allanschwartz/yahrzeit/presentations/yahrzeit_presentation 2015-07-27.pdf

## Yahrzeit Wall Overview

at

## Congregation Beth Sholom

## Yahrzeit/Yizkor presentation

■ | What is a Yahrzeit? What is a Yikzor observance?
■ | Traditional yahrzeit fixtures
■ | New Cong. Beth Sholom requirements:
■ | Ultra-modern building design
■ | Yahrzeit wall, as a architectural entity
■ | Automation, hands free operation
■ | Yahrzeit wall functionality
■ | Yahrzeit Wall is comprised of
■ | Glass Panels
■ | Yahrzeit server software with database and automation
■ | Yahrzeit panel embedded electronics / light modules

## Yahrzeit/Yizkor

■ | A Yahrzeit (yiddish) means time-(of)-year, is the yearly observation of a loved ones’ passing. Rabbinic custom is to say kaddish on the yahrzeit, (or the service immediately before that date), and the mourners often light a 24-hour yahrzeit candle. In addition, the synagogue may light a lamp for the week including the preceeding the Shabbat. These lamps are in yahrzeit fixtures.
■ | On four special yizkor observances per year, all the yahrzeit lamps are illuminating, during the yizkor service. (Yom Kippur, Shmini Atzeret, on the last day of Passover, and on Shavuot). Sometimes we also observe Yom Hazikaron (4th Iyar) and/or Yom Hashoah (27th Nisan).

## Traditional yahrzeit fixtures

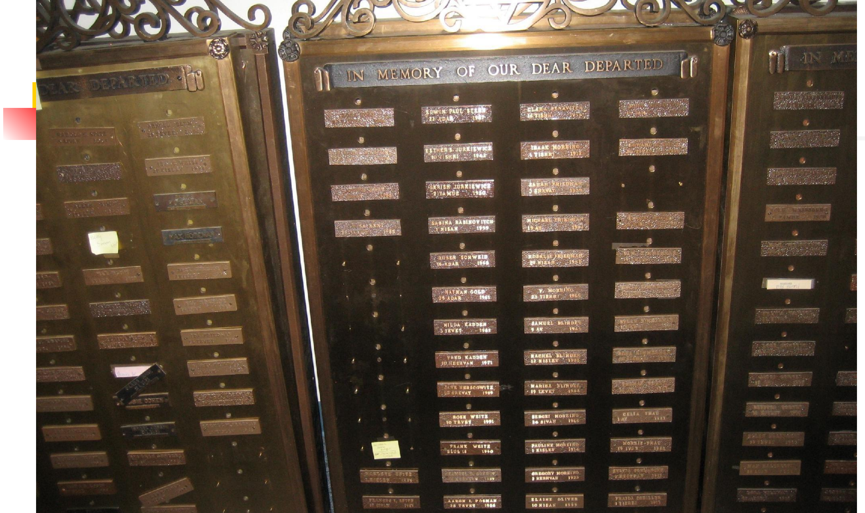
[picture p63: page 4]

## New Cong. Beth Sholom Requirements

## ■ Ultra-modern building design ■ East side of sanctuary has unique features

■ West wall of sanctuary, “Yahrzeit Wall”,

## complements the east wall ■ Etched glass panels appear to float ■ Fully automated LED lamps behind up to 2400 etched names

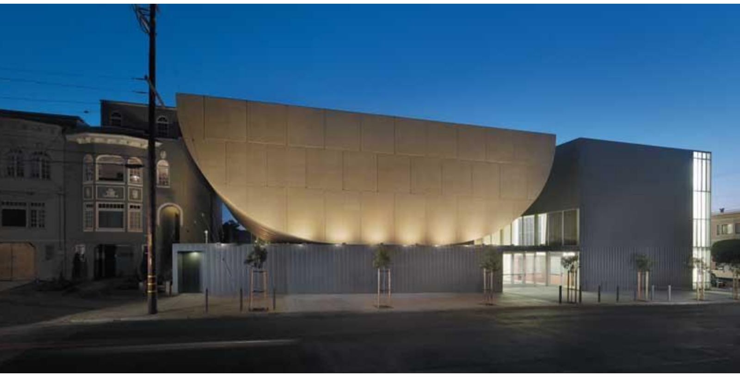
[picture p64: page 6]
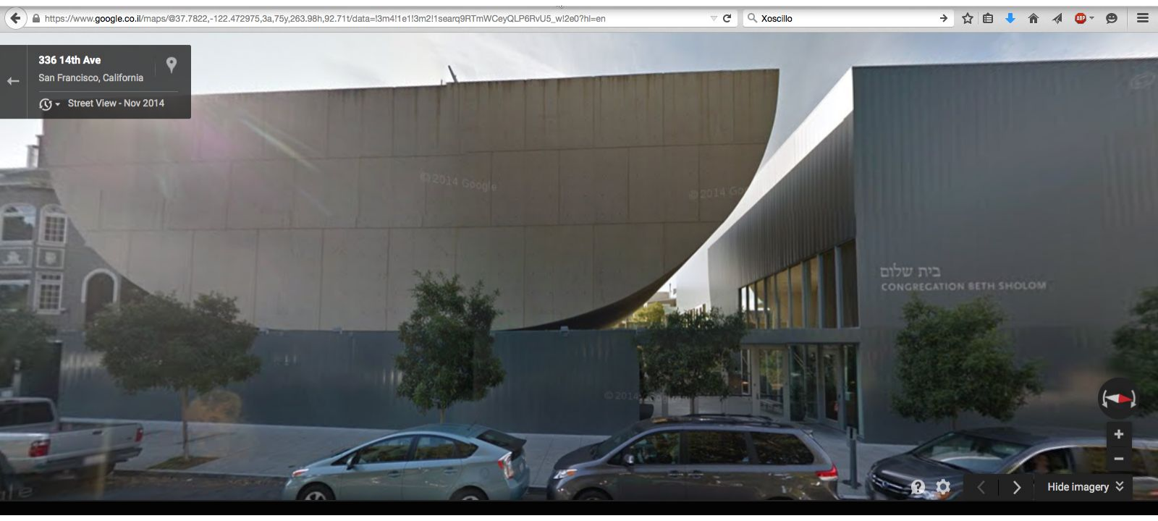
[picture p65: page 7]
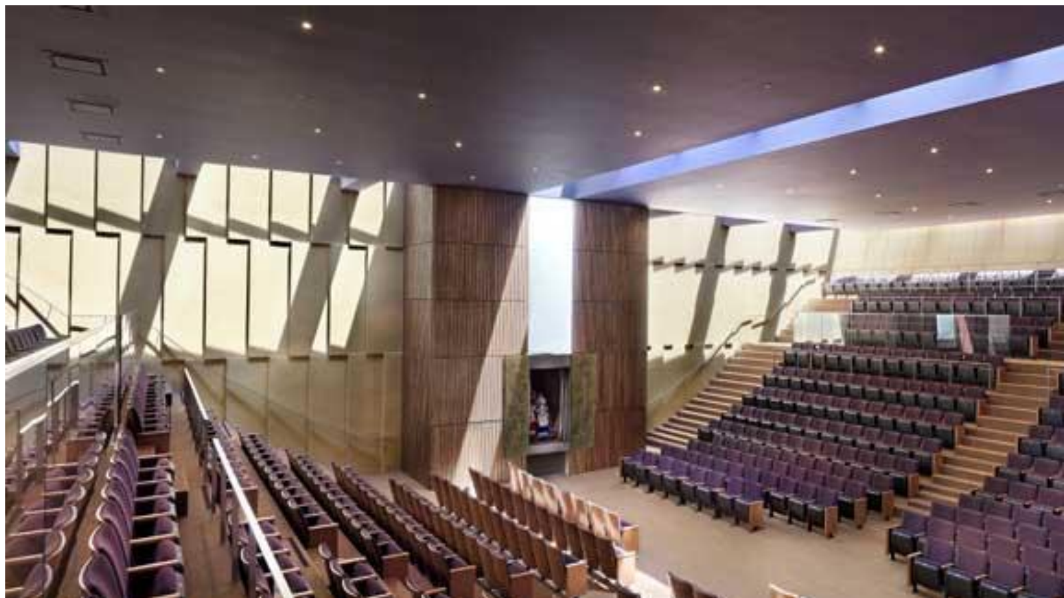
[picture p66: page 8]
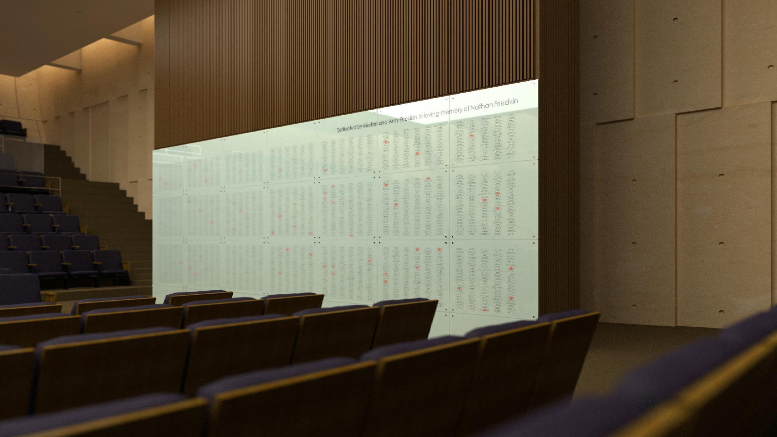
[picture p67: page 9]
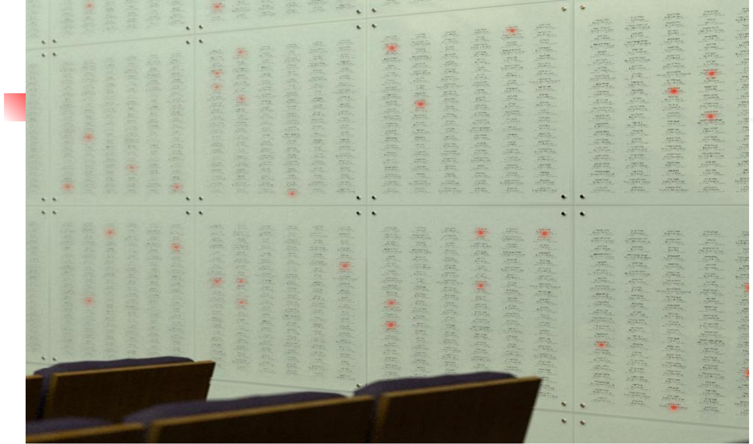
[picture p68: page 10]

# Yahrzeit Wall design goals

## ■ Simplicity & Elegance ■ Ease of use & no maintenance ■ Full database integration & automation ■ Future proof

# Yahrzeit Wall components

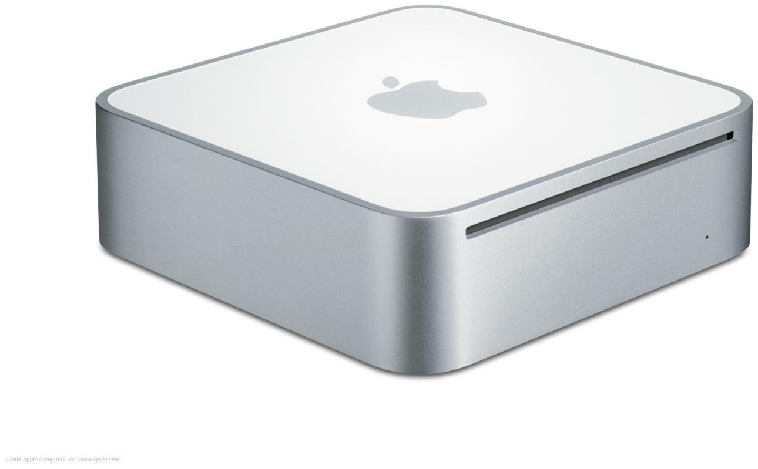
[picture p69: figure]
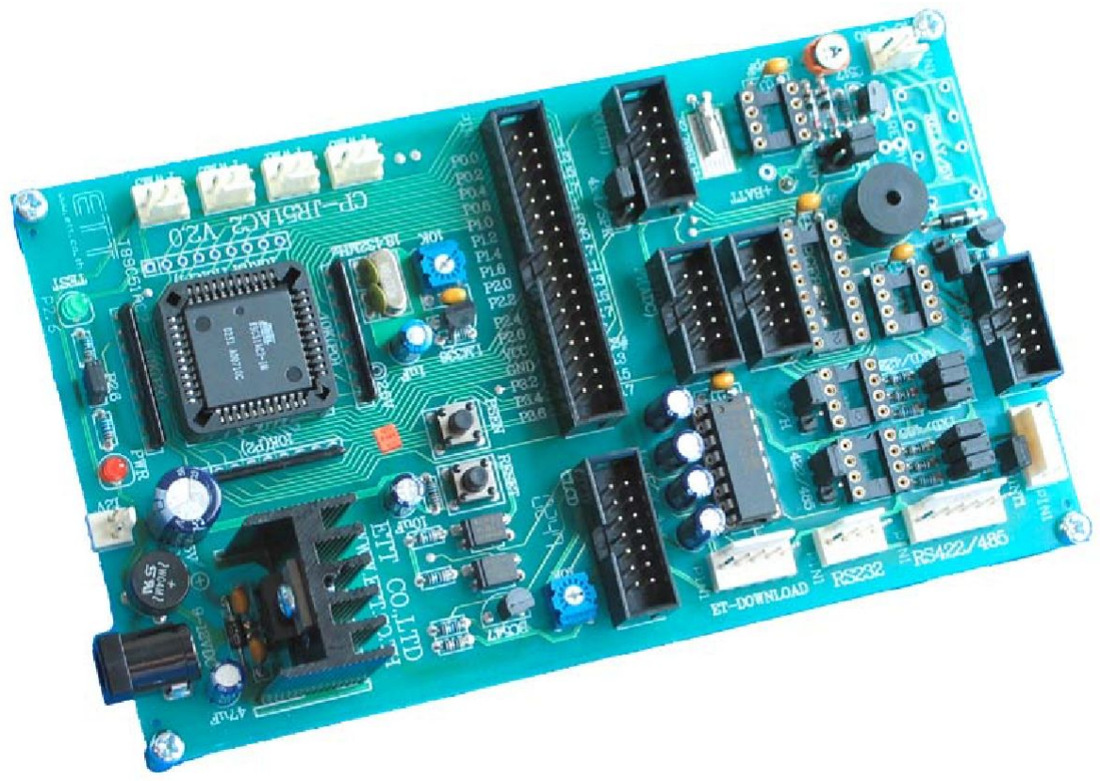
[picture p70: figure]
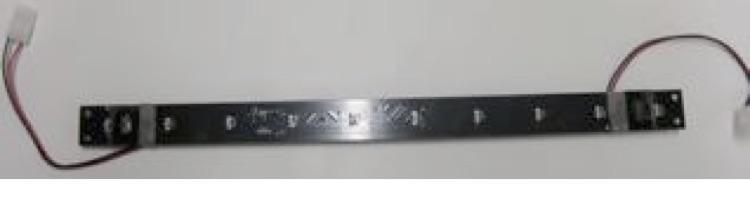
[picture p71: figure]
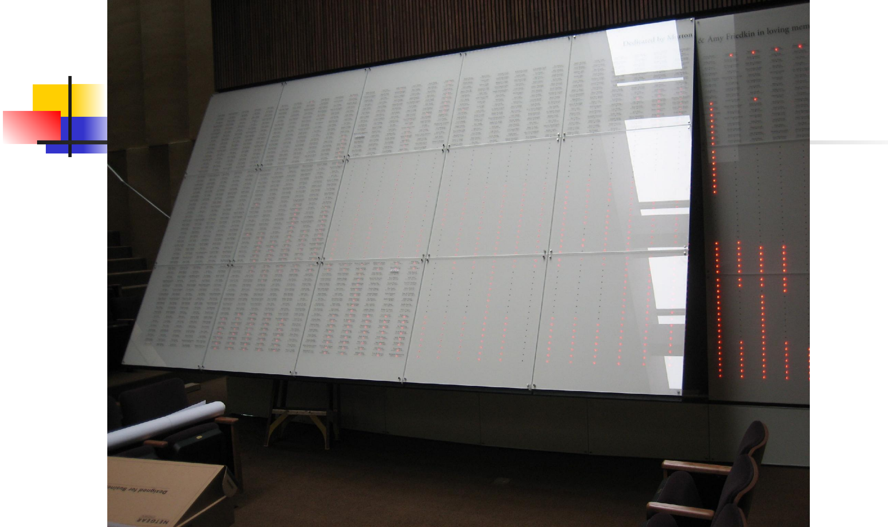
[picture p72: page 13]
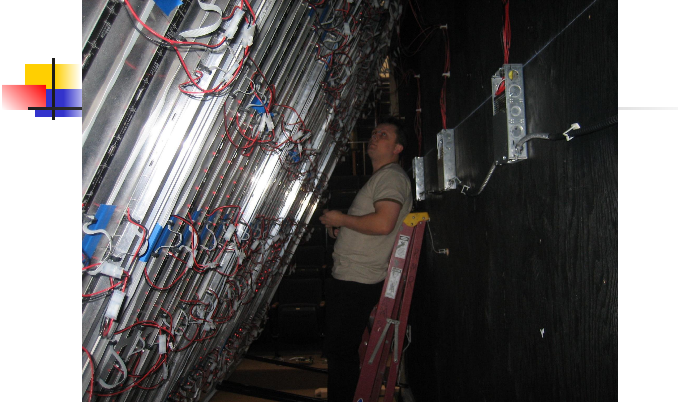
[picture p73: page 14]

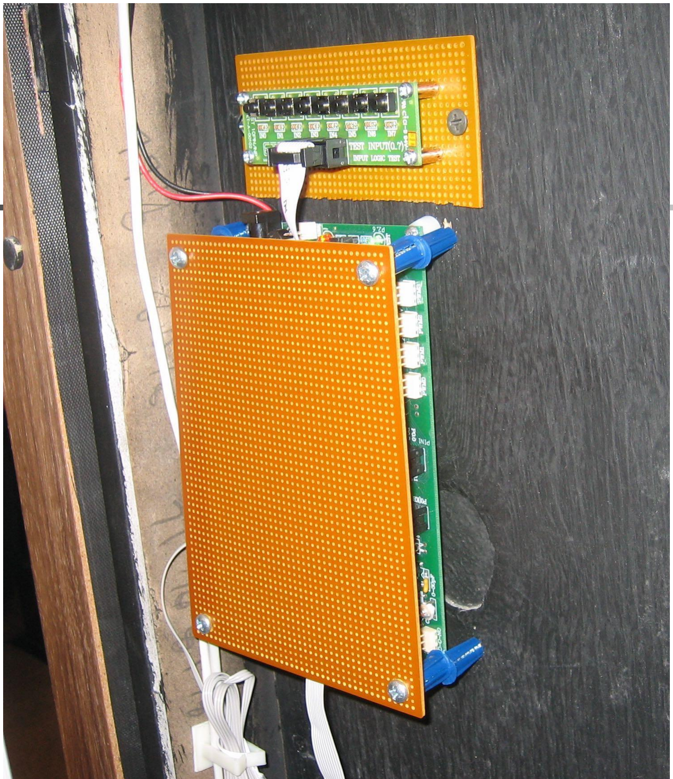
[picture p74: figure]

# Yahrzeit V2 (2015) components

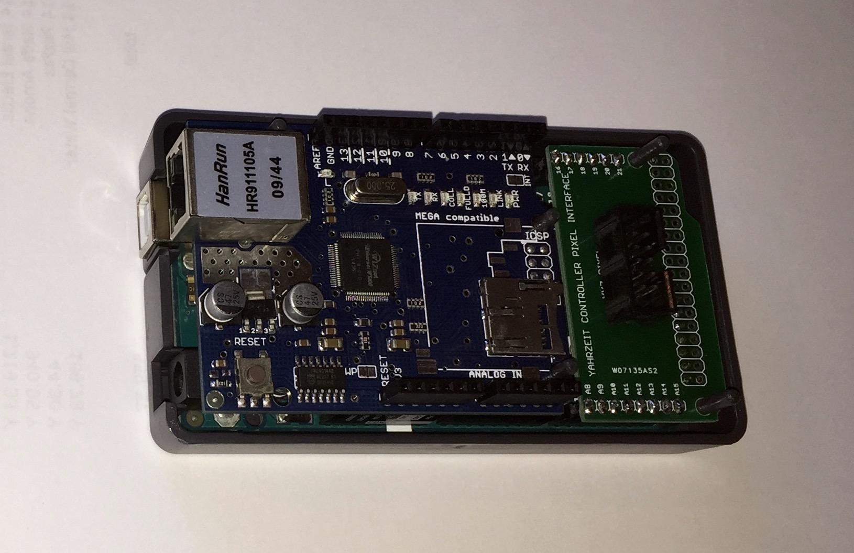
[picture p75: figure]
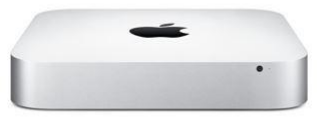
[picture p76: figure]

## Yahrzeit controller software

## ■ Jewish-calendar based yahrzeit light automation ■ Ability to maintain the memorial database ■ Customize yahrzeit observance for any name ■ Customize the synagogues yahrzeit and yizkor observances based on Conservative / Orthodox / Reform minhag

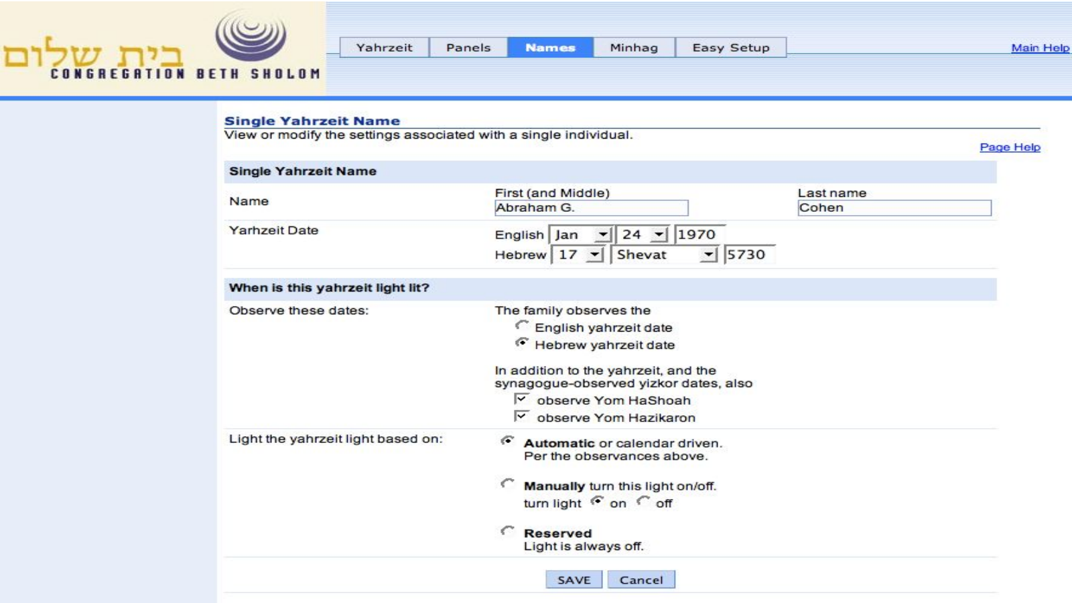
[picture p77: page 18]
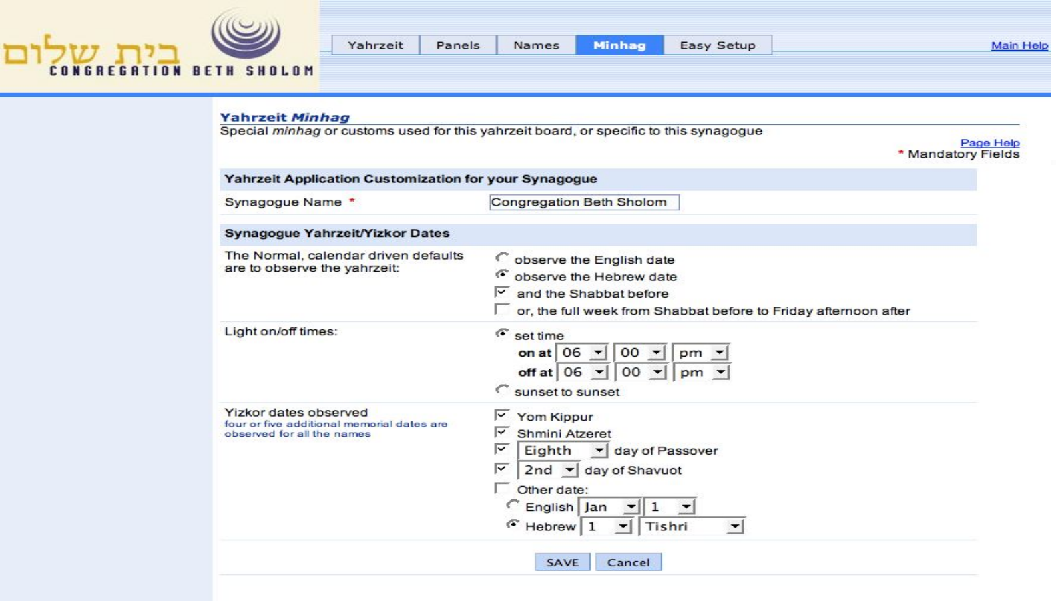
[picture p78: page 19]
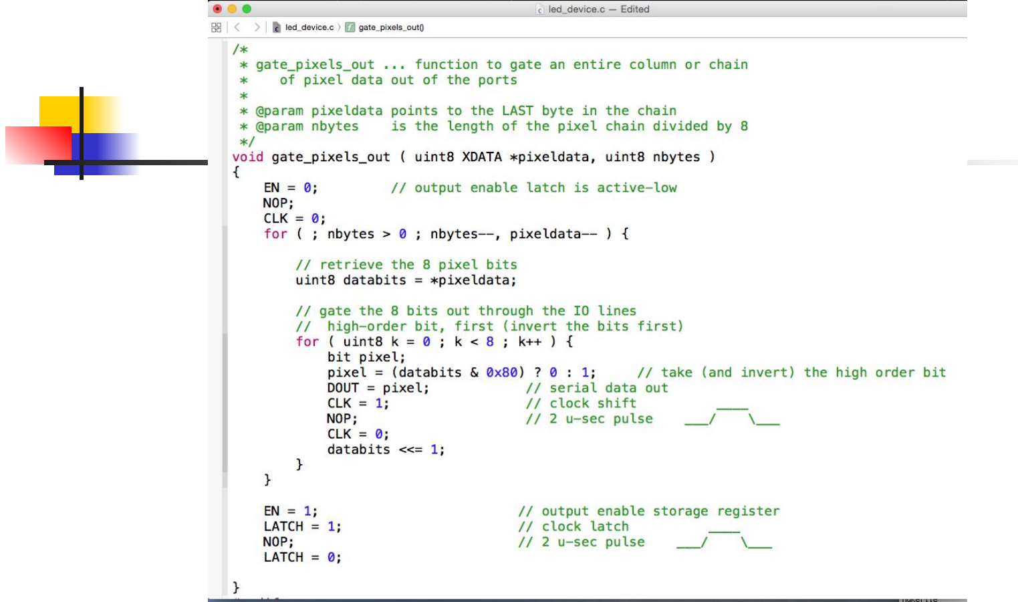
[picture p79: page 20]
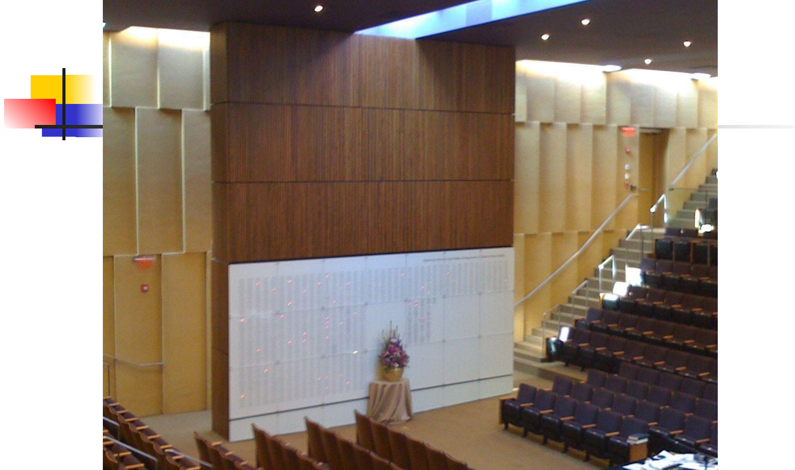
[picture p80: page 21]
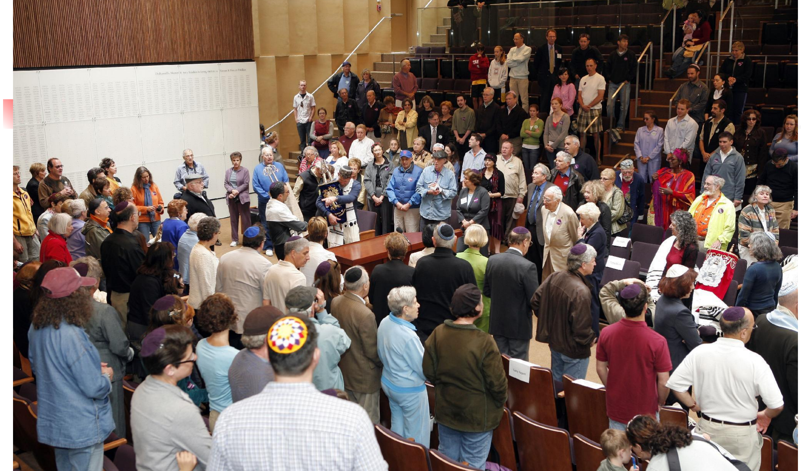
[picture p81: page 22]
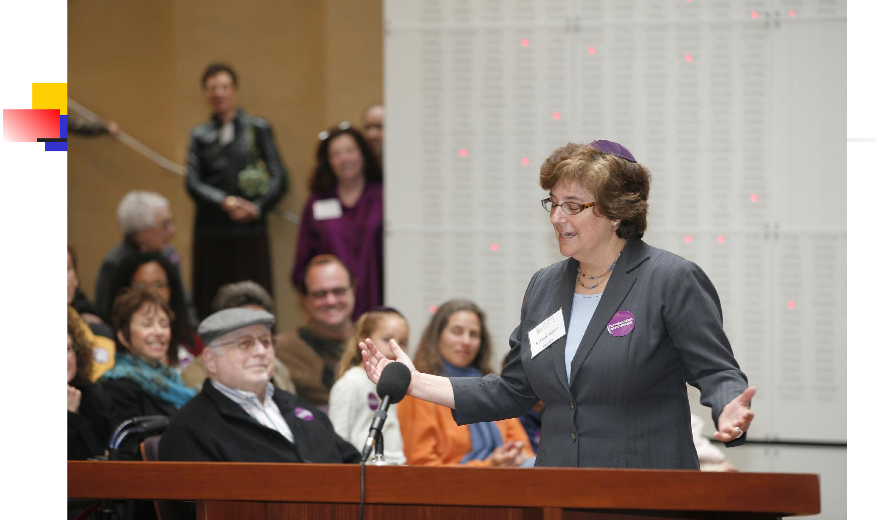
[picture p82: page 23]
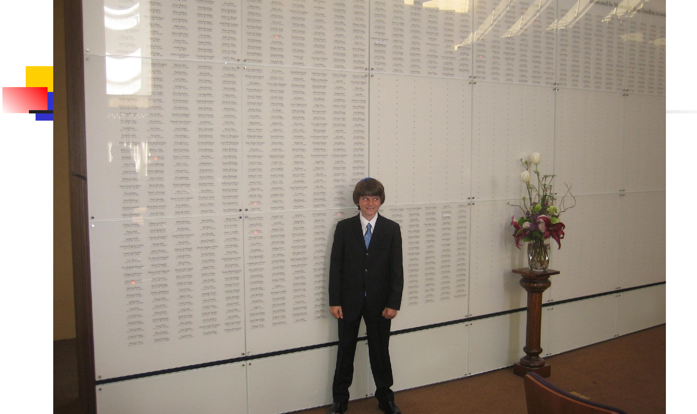
[picture p83: page 24]

# Thank you

## ■ Sources at: ■ https://github.com/allanschwartz/yahrzeit
