allanschwartz/yahrzeit/presentations/presentation_images_used/T89C51 Training Board - V5.pdf

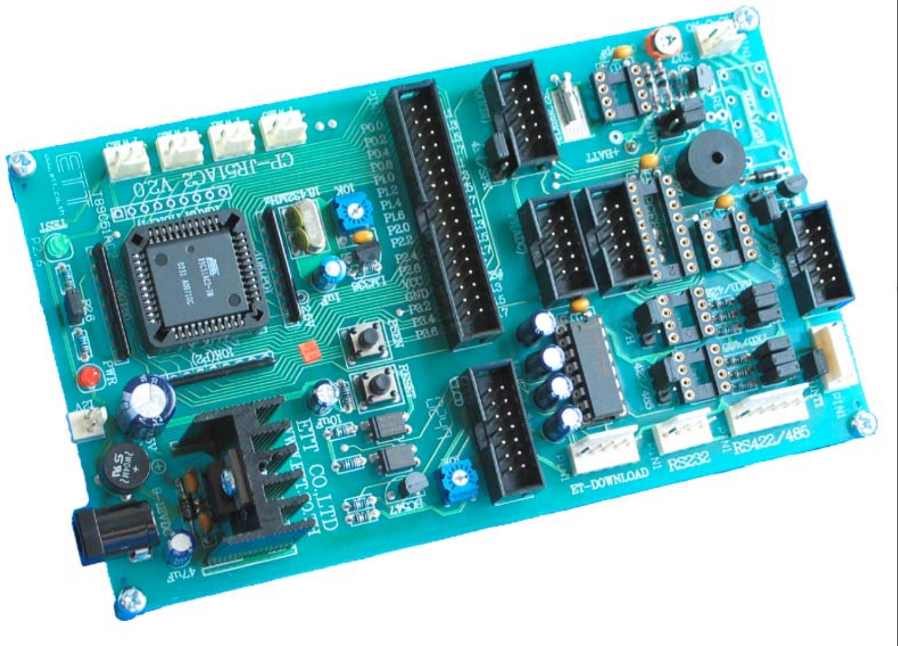
[picture p84: page 1]
