allanschwartz/yahrzeit/Hardware/cables/molex_5559-03P.JPG

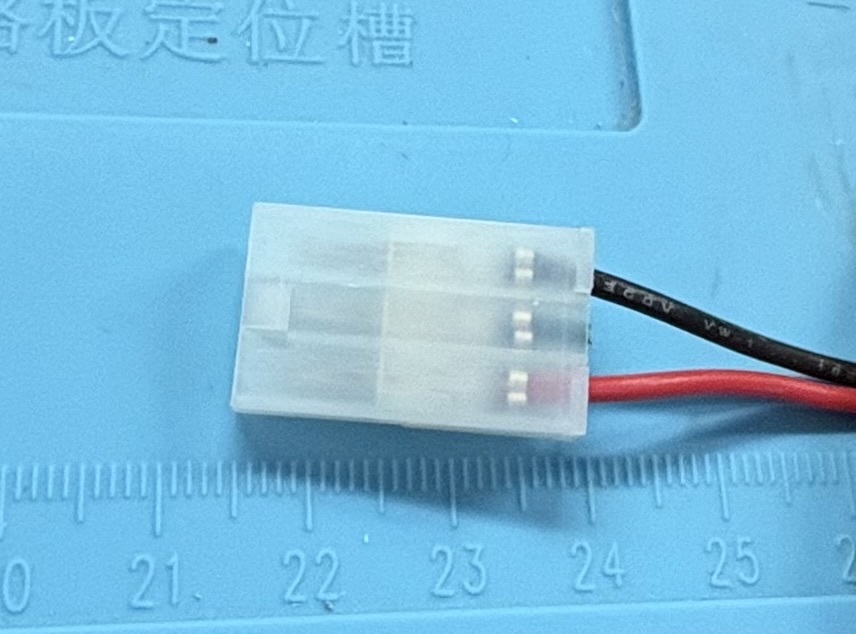
Hardware/cables/molex_5559-03P.JPG
