allanschwartz/yahrzeit/Hardware/pixel_interface_v3/pixel_interface_v3-schematic.png

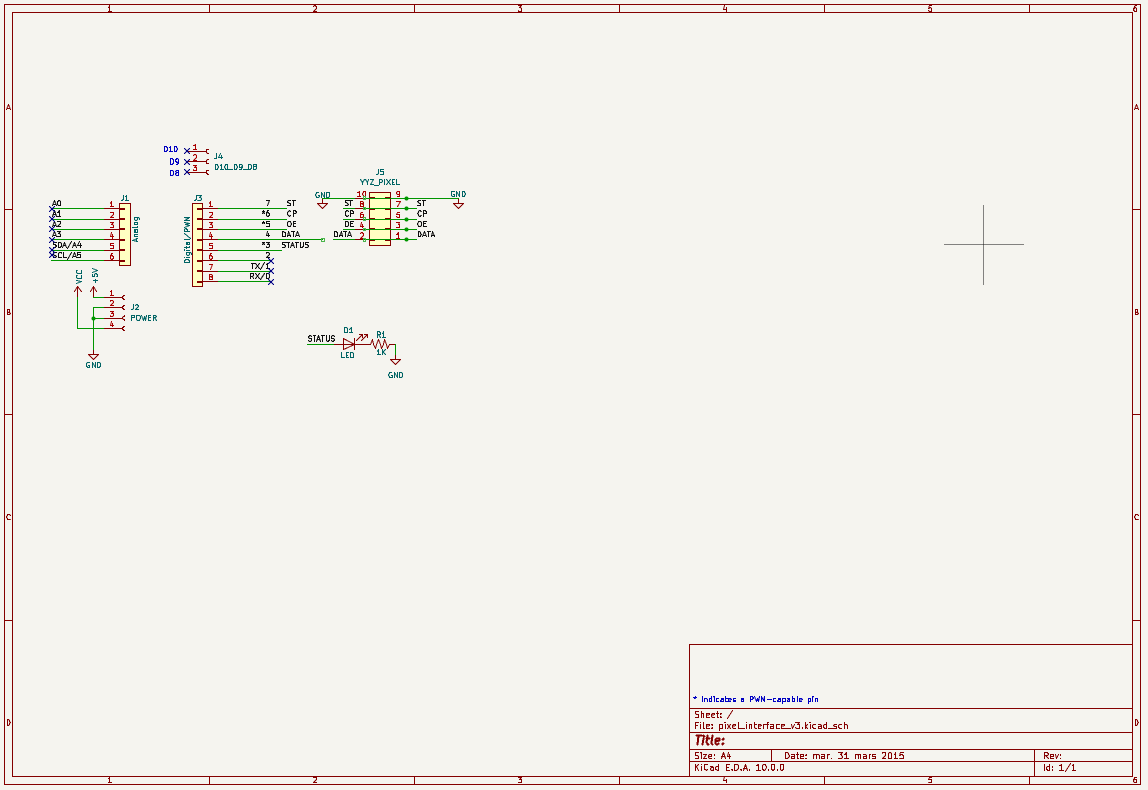
Hardware/pixel_interface_v3/pixel_interface_v3-schematic.png
