allanschwartz/yahrzeit/Hardware/YYZ_SHIELD_v2/arduino_shield.PNG

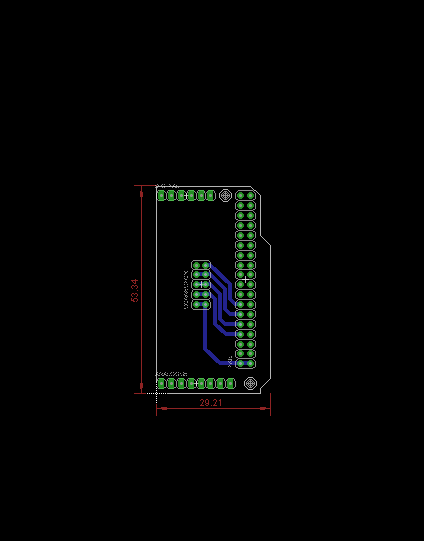
Hardware/YYZ_SHIELD_v2/arduino_shield.PNG
