allanschwartz/yahrzeit/Hardware/YYZ_SHIELD_v2/prototype assm2.jpg

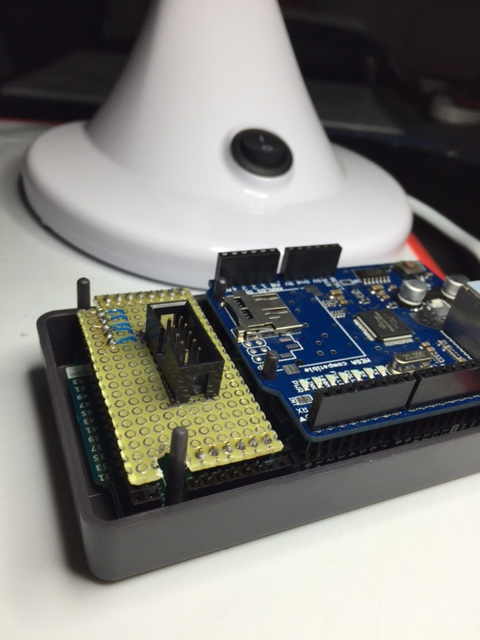
Hardware/YYZ_SHIELD_v2/prototype assm2.jpg
