allanschwartz/yahrzeit/Hardware/YYZ_SHIELD_v2/prototype tail shield.JPG

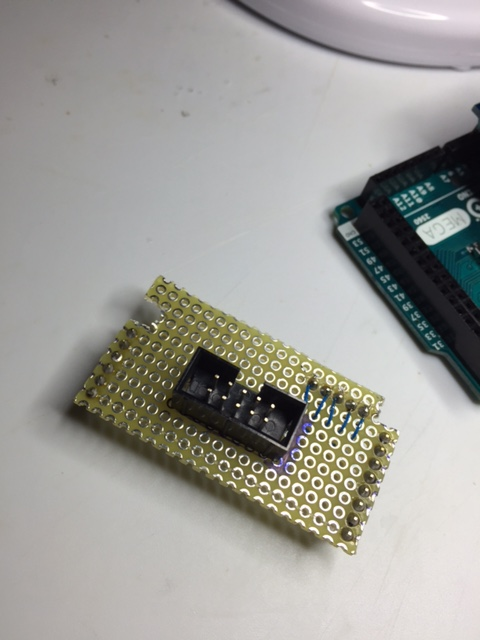
Hardware/YYZ_SHIELD_v2/prototype tail shield.JPG
