allanschwartz/yahrzeit/Hardware/YYZ_SHIELD_v2/shield modified.PNG

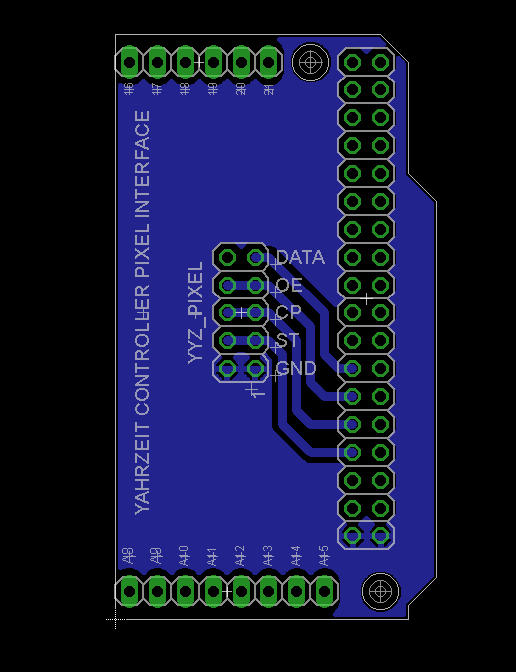
Hardware/YYZ_SHIELD_v2/shield modified.PNG
