allanschwartz/yahrzeit/Hardware/YYZ_SHIELD_v2/yarhzeit_adapter_shield_bb.jpg

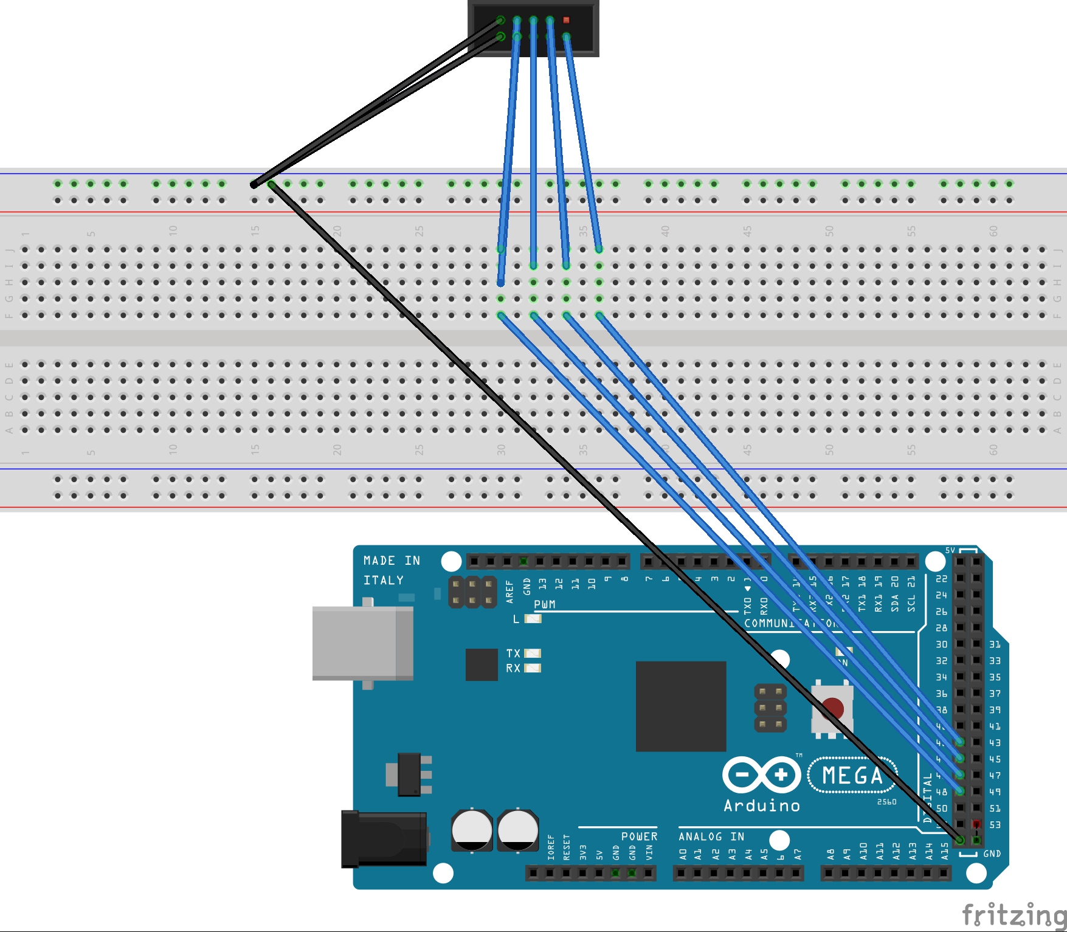
Hardware/YYZ_SHIELD_v2/yarhzeit_adapter_shield_bb.jpg
