allanschwartz/yahrzeit/presentations/other_images/finished yahrzeit embedded controller.jpg

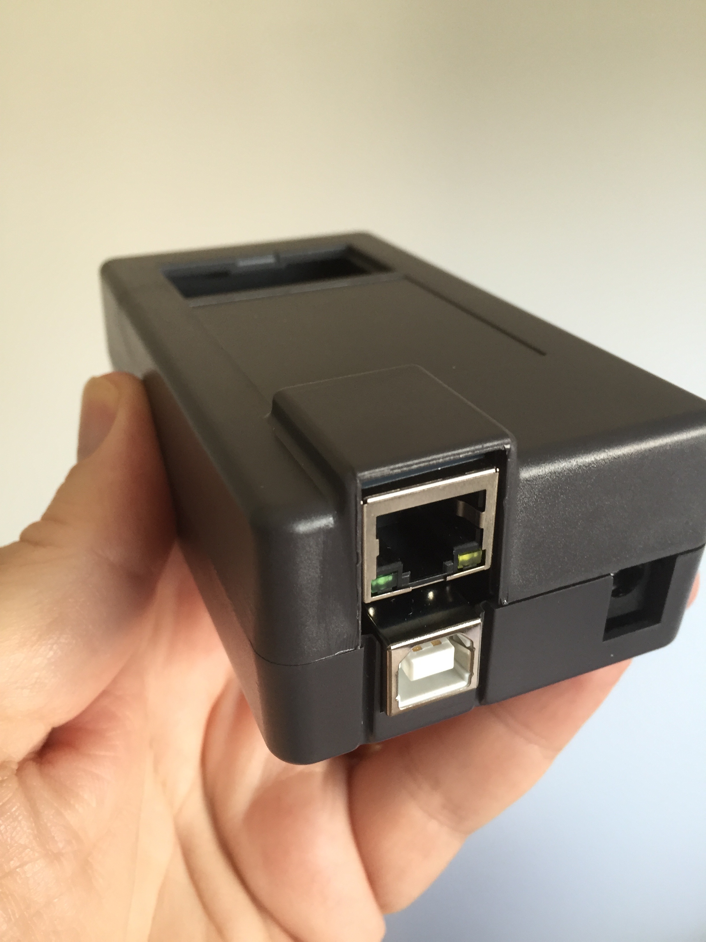
presentations/other_images/finished yahrzeit embedded controller.jpg
