allanschwartz/yahrzeit/presentations/other_images/image-21panels.jpg

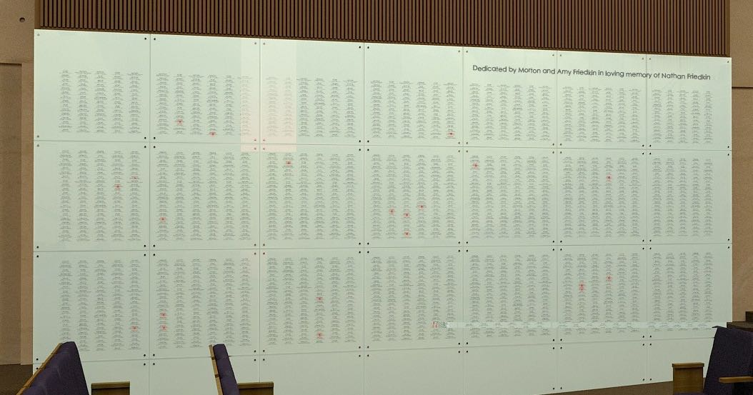
presentations/other_images/image-21panels.jpg
