allanschwartz/yahrzeit/presentations/other_images/IMG_0024.jpg

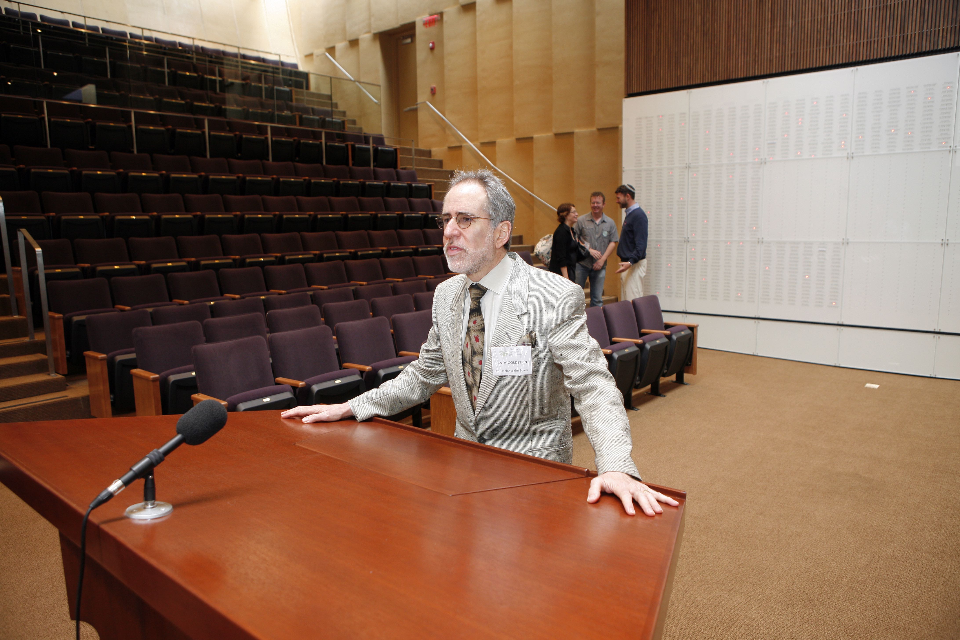
presentations/other_images/IMG_0024.jpg
