allanschwartz/yahrzeit/presentations/other_images/IMG_0146.jpg

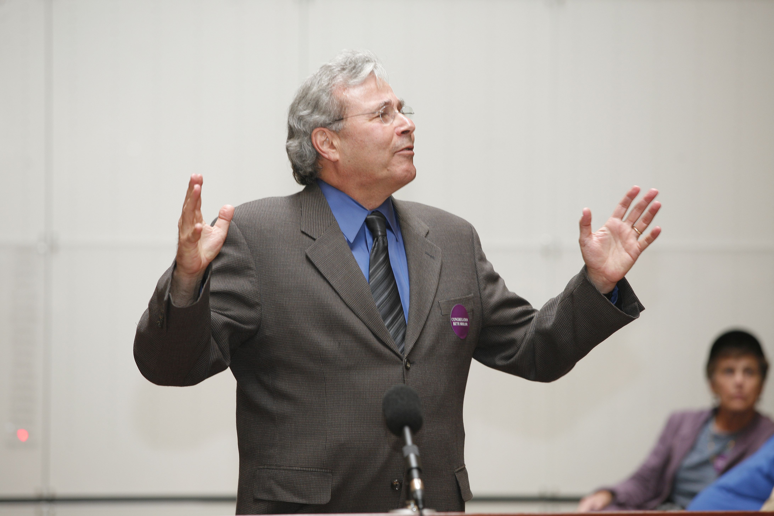
presentations/other_images/IMG_0146.jpg
