allanschwartz/yahrzeit/presentations/presentation_images_used/_MG_0129.jpg

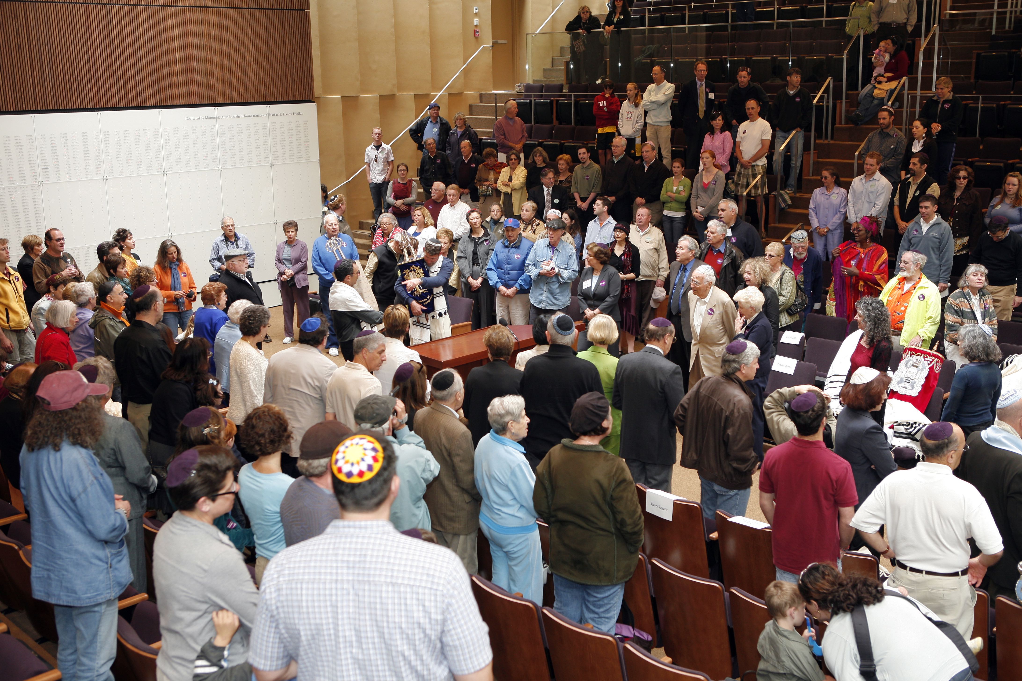
presentations/presentation_images_used/_MG_0129.jpg
