allanschwartz/yahrzeit/presentations/presentation_images_used/digionesp.jpg

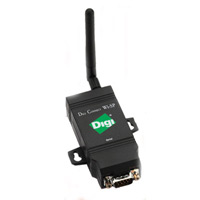
presentations/presentation_images_used/digionesp.jpg
