allanschwartz/yahrzeit/presentations/presentation_images_used/macmini2007.jpg

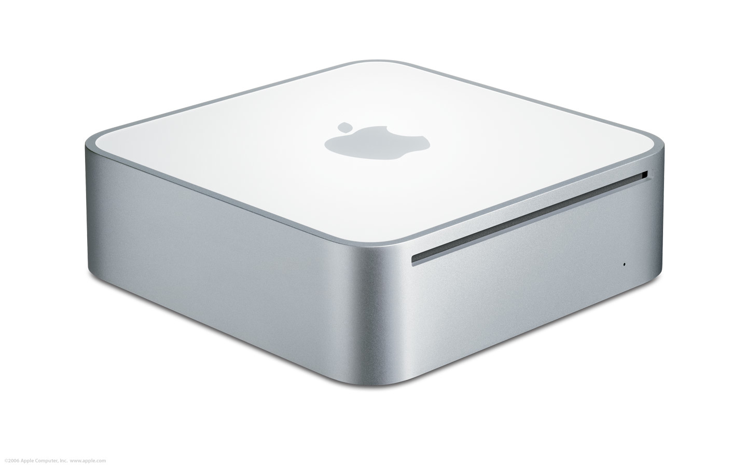
presentations/presentation_images_used/macmini2007.jpg
