allanschwartz/yahrzeit/presentations/presentation_images_used/macmini2015.jpg

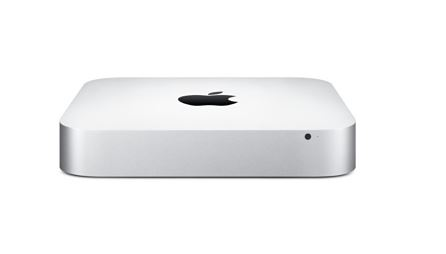
presentations/presentation_images_used/macmini2015.jpg
