allanschwartz/yahrzeit/yahrzeit_site-v3/images/FullBoardx200.jpg

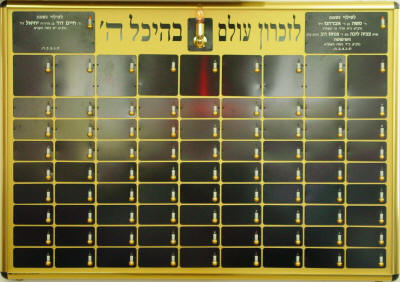
yahrzeit_site-v3/images/FullBoardx200.jpg
