allanschwartz/yahrzeit/yahrzeit_site-v3/screenshots/Screenshot 1panels.png

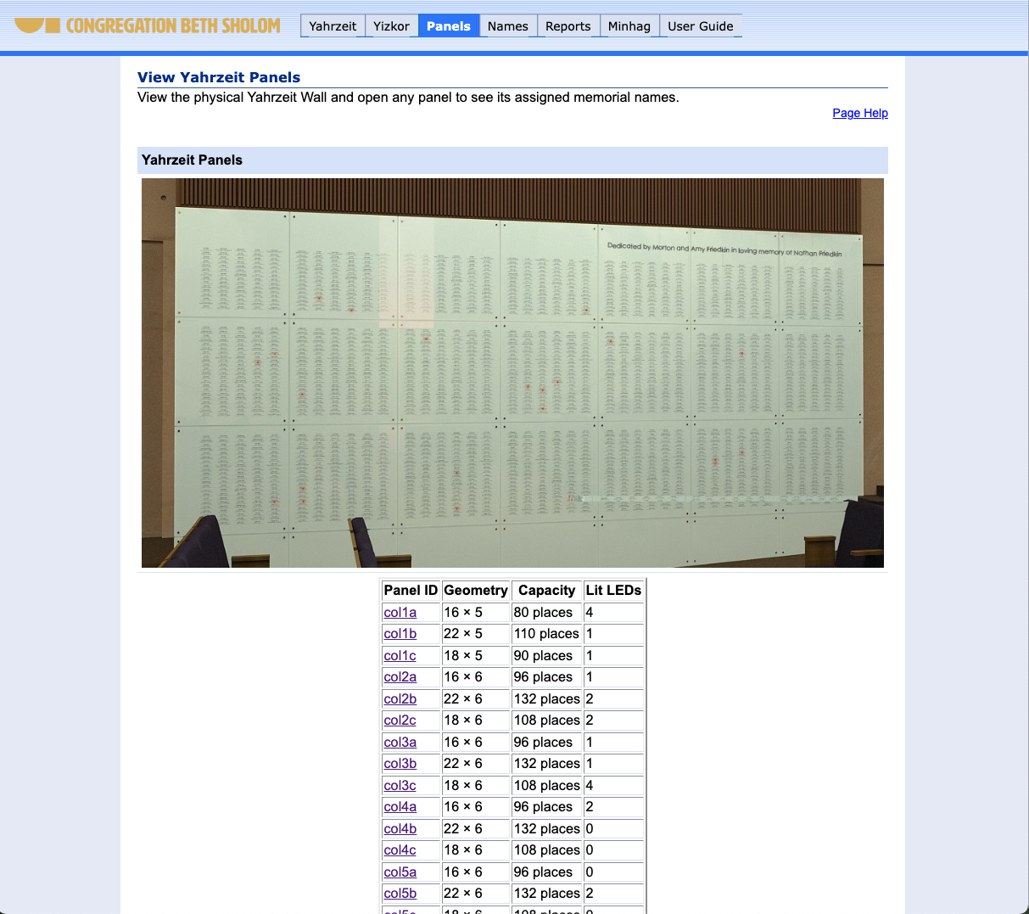
yahrzeit_site-v3/screenshots/Screenshot 1panels.png
