allanschwartz/yahrzeit/Hardware/3D Printing/yahrzeit_controller_case.jpg

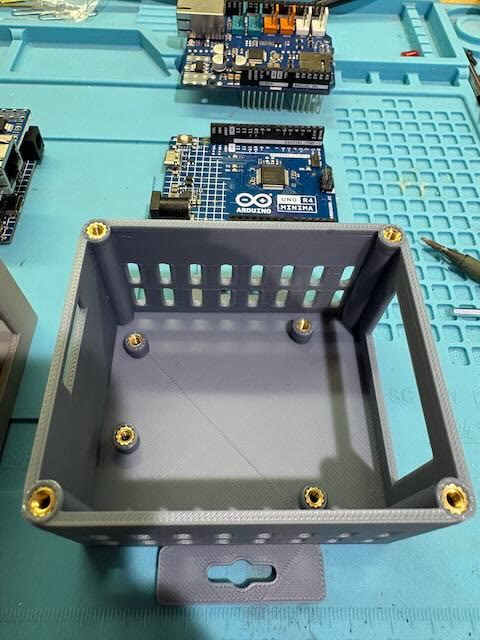
Hardware/3D Printing/yahrzeit_controller_case.jpg
