allanschwartz/yahrzeit/presentations/other_images/assembled yyz IF board.JPG

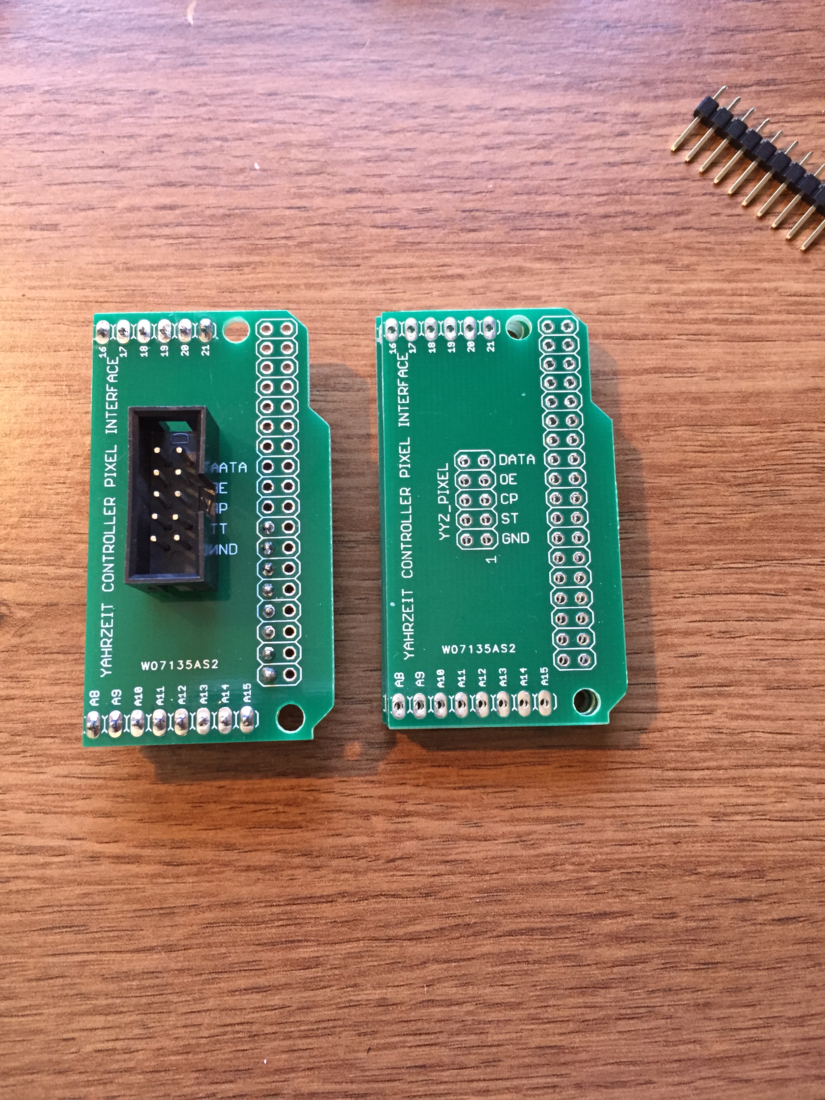
presentations/other_images/assembled yyz IF board.JPG
