allanschwartz/yahrzeit/presentations/other_images/bench setup w saleae.jpg

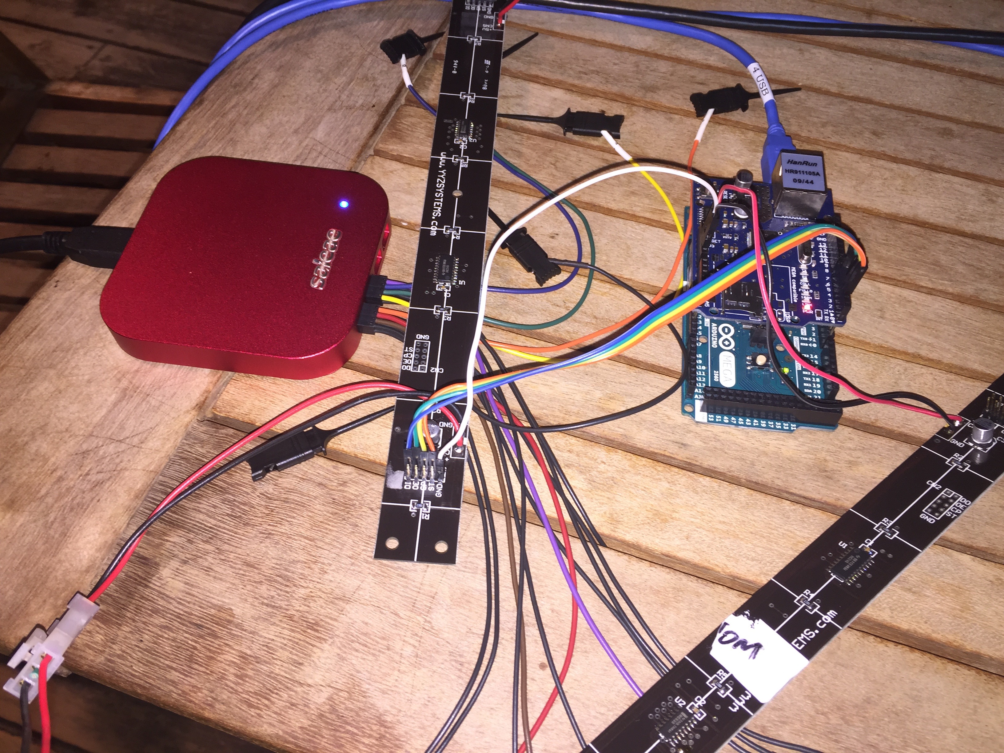
presentations/other_images/bench setup w saleae.jpg
