allanschwartz/yahrzeit/Hardware/yahrzeit_pixel9/yahrzeit_pixel9-schematic.pdf

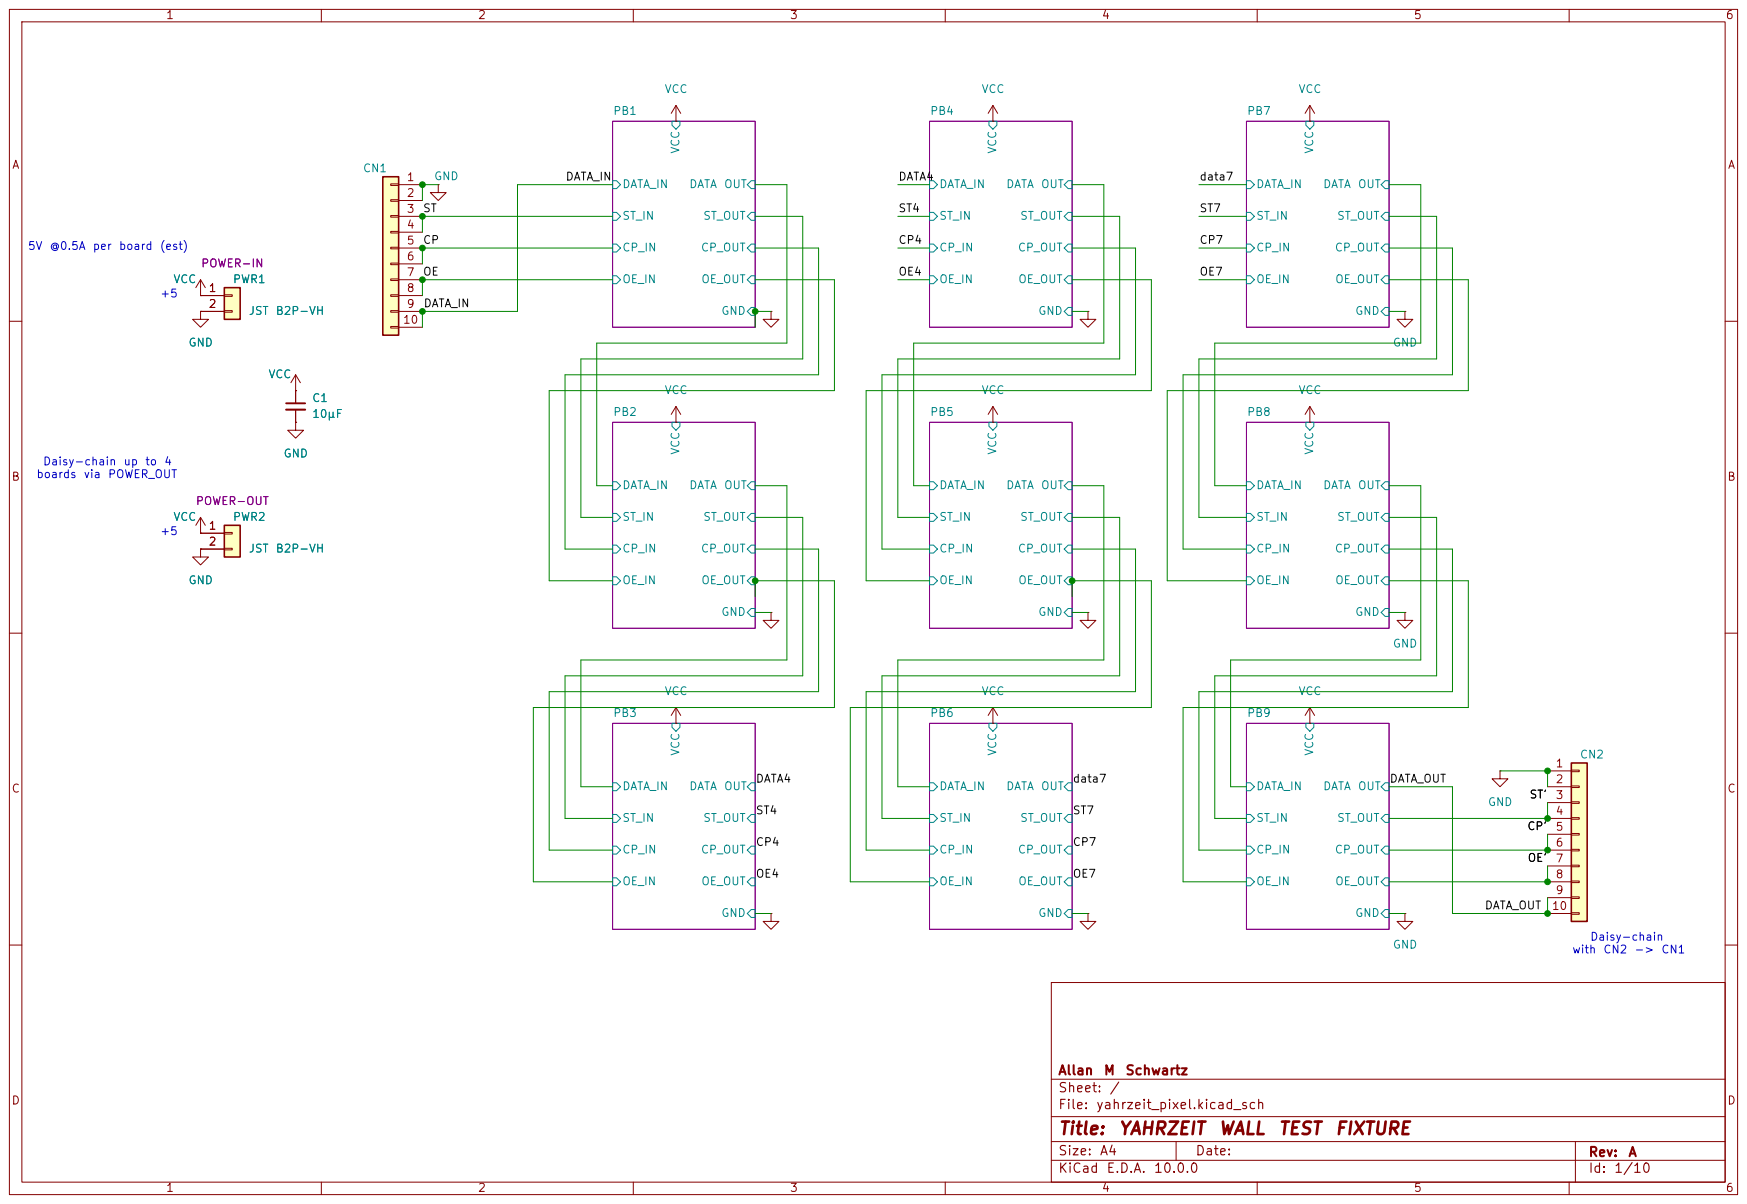
[picture p125: page 1]

boards via POWER_OUT 5V @0.5A per board (est)GND

with CN2 -> CN1 +5 Daisy-chain up to 4

Sheet: /
File: yahrzeit_pixel.kicad_sch
Title: YAHRZEIT WALL TEST FIXTURE

Size: A4 | Rev: A
KiCad E.D.A. 10.0.0 | Id: 1/10

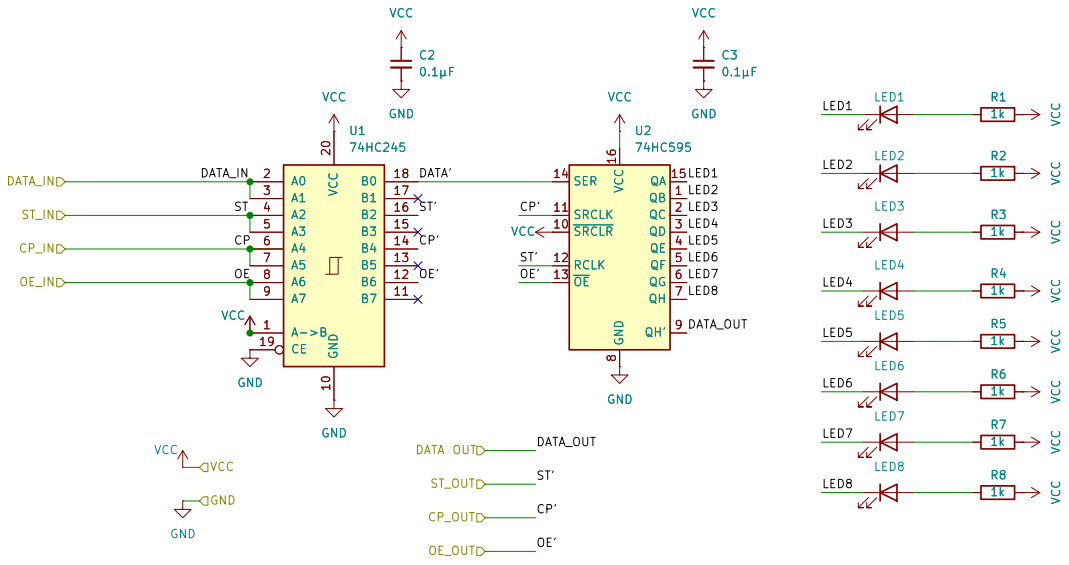
[picture p126: page 2]

Allan M Schwartz
Sheet: /PB1/
File: pblock.kicad_sch
Title: YAHRZEIT WALL TEST FIXTURE

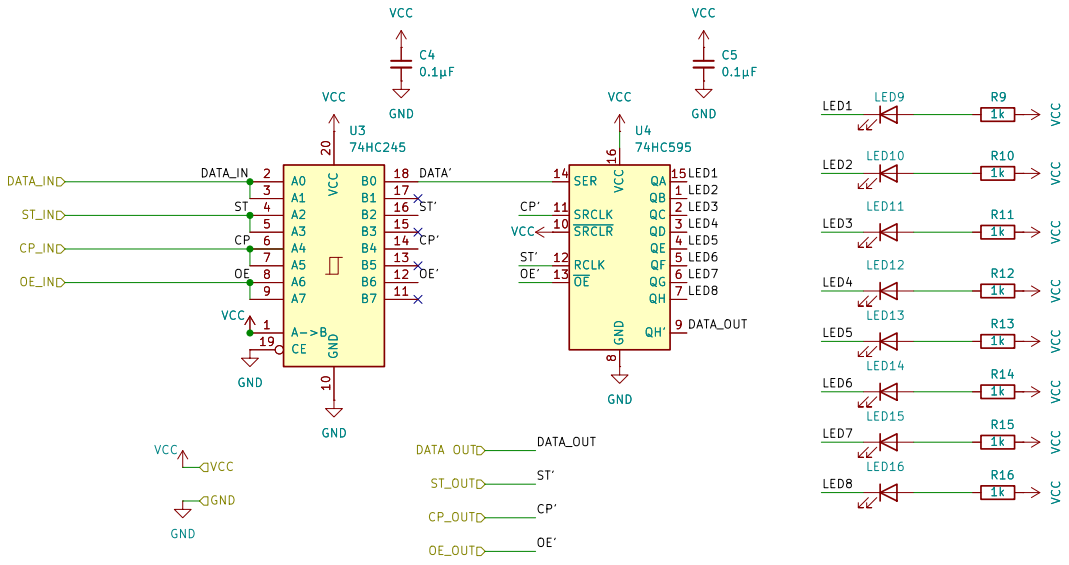
[picture p127: page 3]

Sheet: /PB2/
File: pblock.kicad_sch
Title: YAHRZEIT WALL TEST FIXTURE

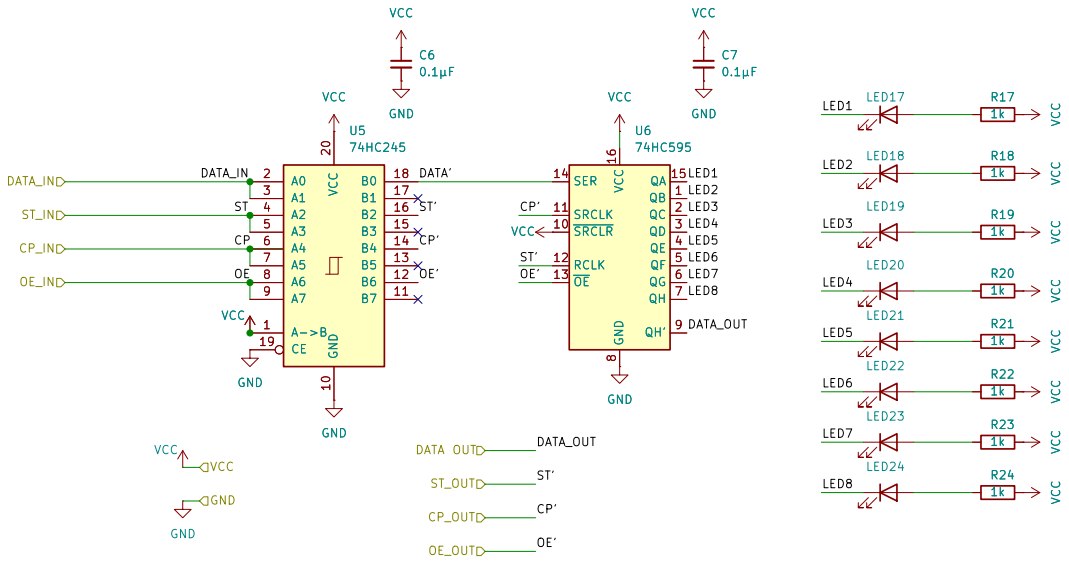
[picture p128: page 4]

Sheet: /PB3/
File: pblock.kicad_sch
Title: YAHRZEIT WALL TEST FIXTURE

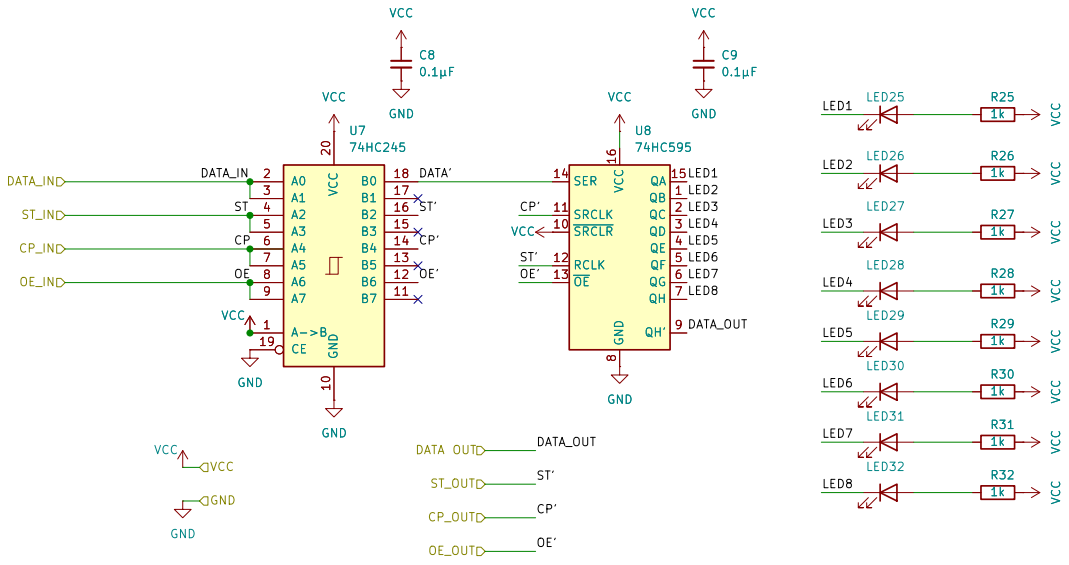
[picture p129: page 5]

Allan M Schwartz
Sheet: /PB4/
File: pblock.kicad_sch
Title: YAHRZEIT WALL TEST FIXTURE

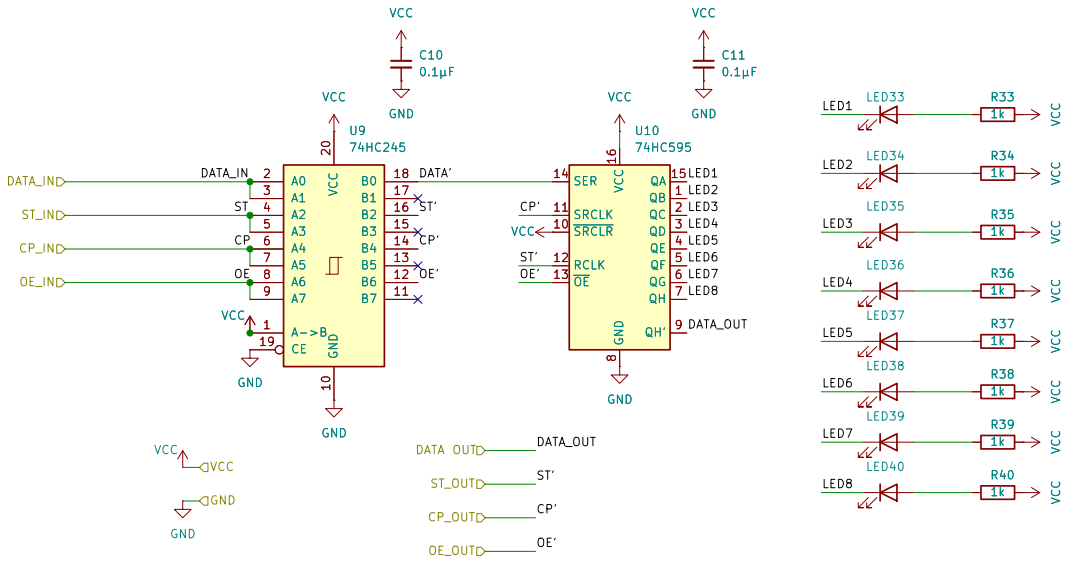
[picture p130: page 6]

Allan M Schwartz
Sheet: /PB5/
File: pblock.kicad_sch
Title: YAHRZEIT WALL TEST FIXTURE

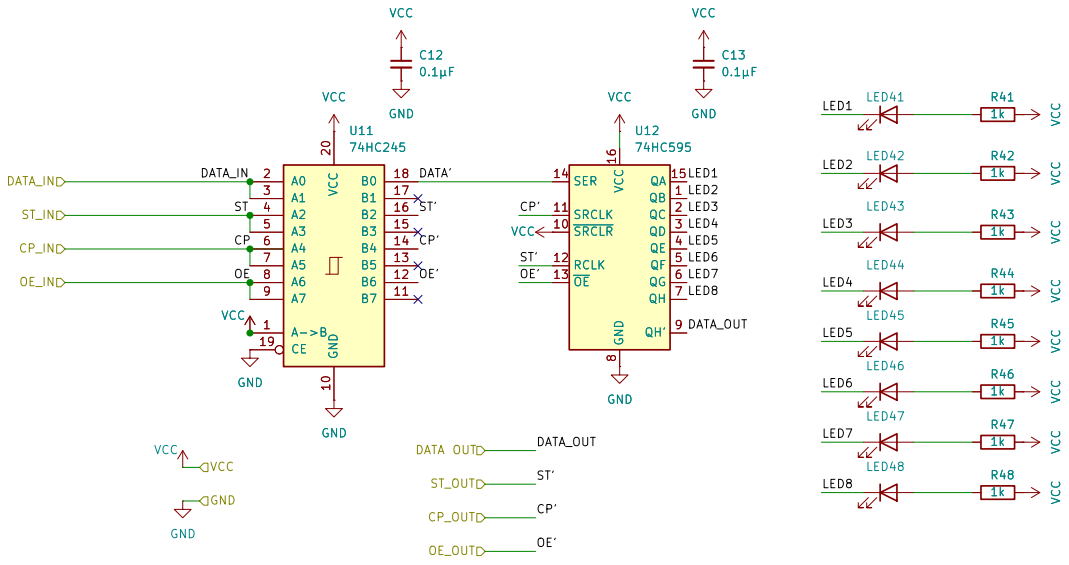
[picture p131: page 7]

Allan M Schwartz
Sheet: /PB6/
File: pblock.kicad_sch
Title: YAHRZEIT WALL TEST FIXTURE

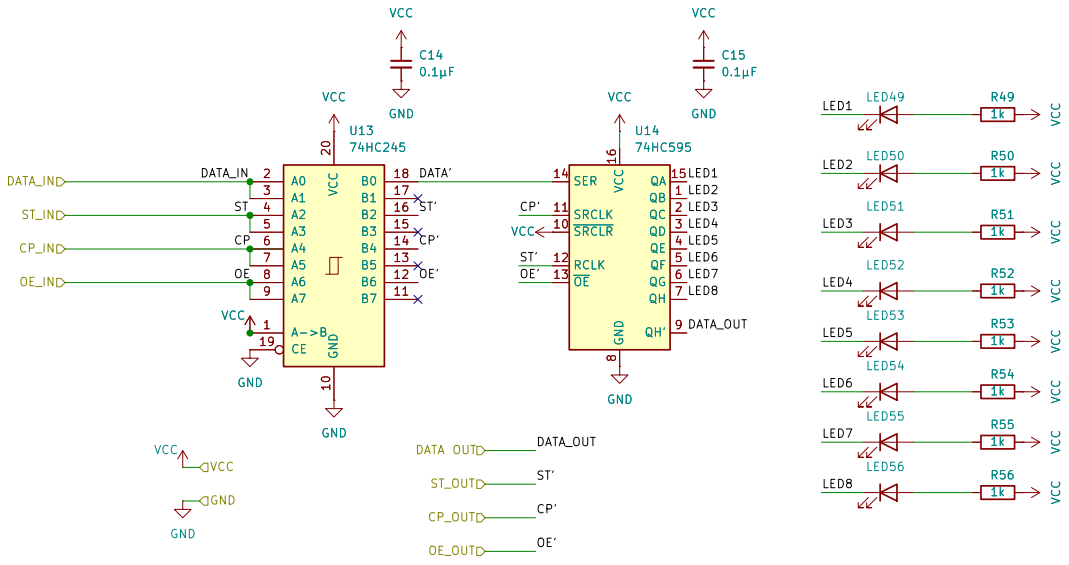
[picture p132: page 8]

Sheet: /PB7/
File: pblock.kicad_sch
Title: YAHRZEIT WALL TEST FIXTURE

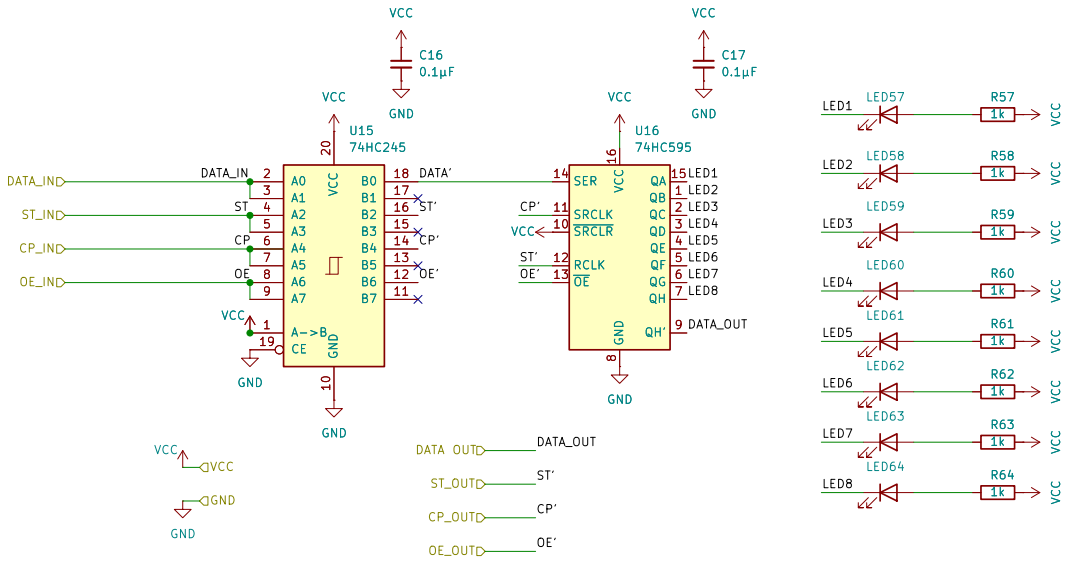
[picture p133: page 9]

Sheet: /PB8/
File: pblock.kicad_sch
Title: YAHRZEIT WALL TEST FIXTURE

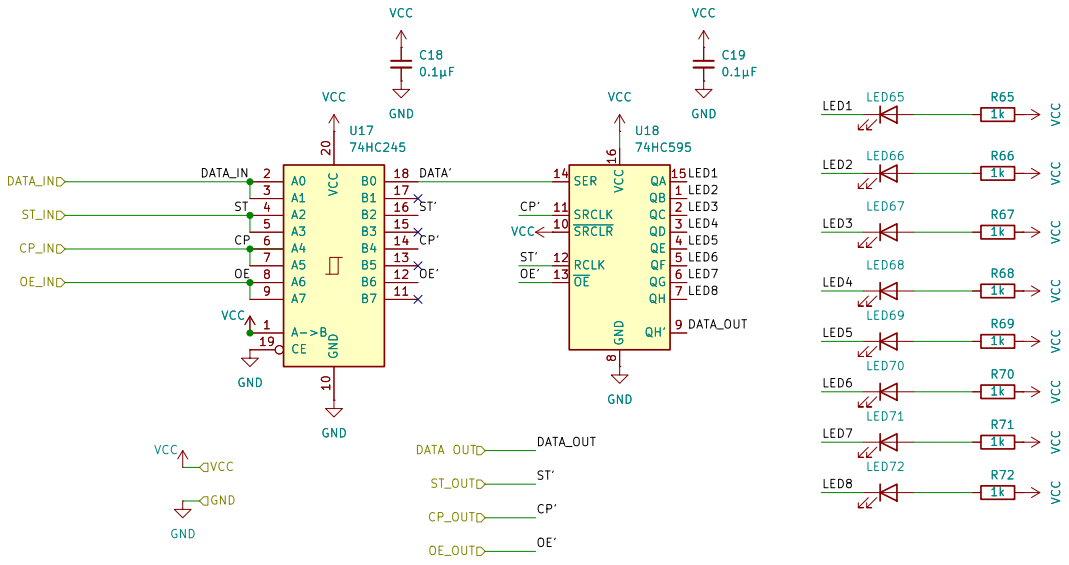
[picture p134: page 10]

Allan M Schwartz
Sheet: /PB9/
File: pblock.kicad_sch
Title: YAHRZEIT WALL TEST FIXTURE
