allanschwartz/yahrzeit/Hardware/schematics/Schematic_yyz_pixel.pdf

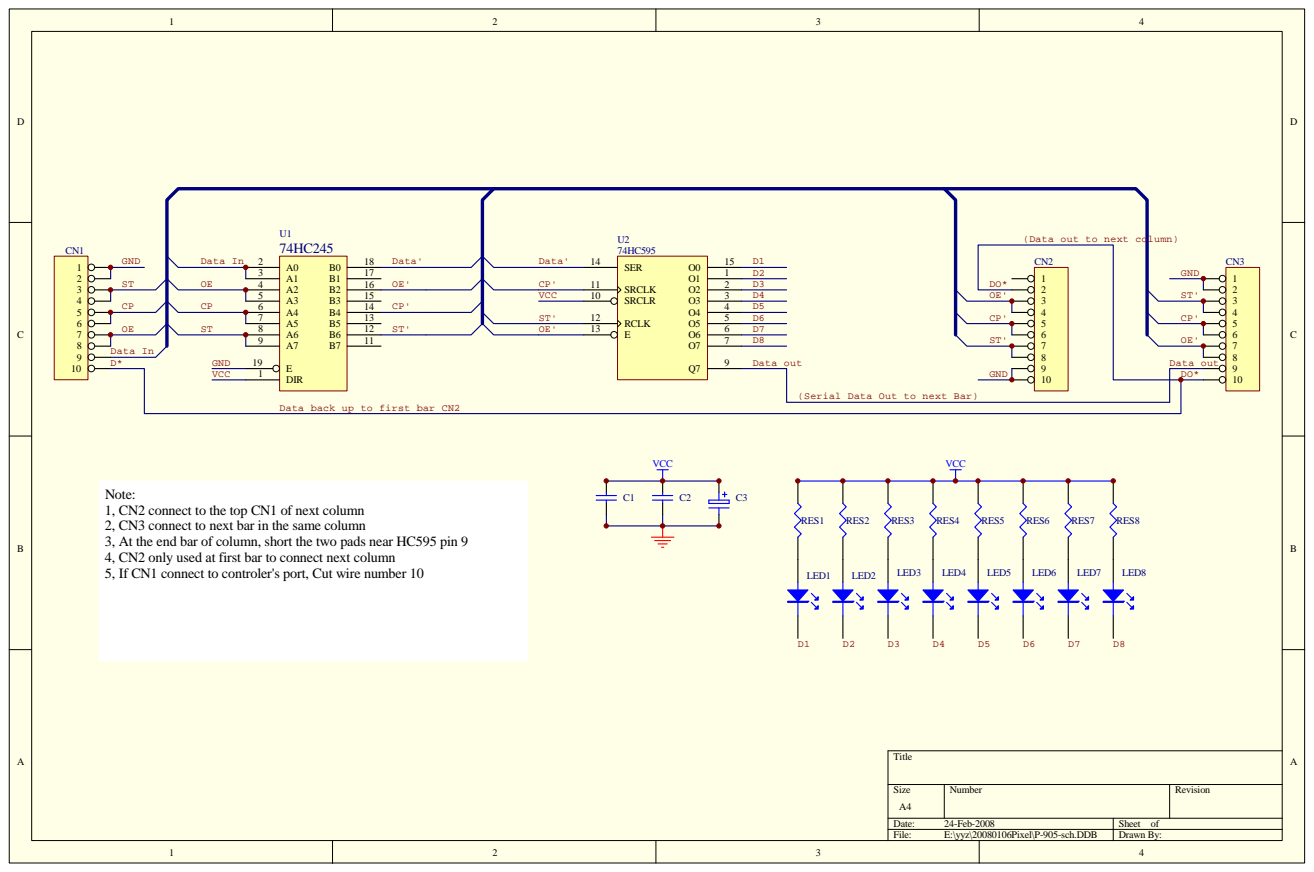
[picture p135: page 1]

(Data out to next column)

(Serial Data Out to next Bar)

Data back up to first bar CN2

Note:
1, CN2 connect to the top CN1 of next column
2, CN3 connect to next bar in the same column
3, At the end bar of column, short the two pads near HC595 pin 9
4, CN2 only used at first bar to connect next column
5, If CN1 connect to controler's port, Cut wire number 10

Size A4 | Number | Revision

Date: 24-Feb-2008 | Sheet of
File: E:\yyz\20080106Pixel\P-905-sch.DDB | Drawn By:
