allanschwartz/yahrzeit/panels/panels-2008-08/panel-col5b-noleds.pdf

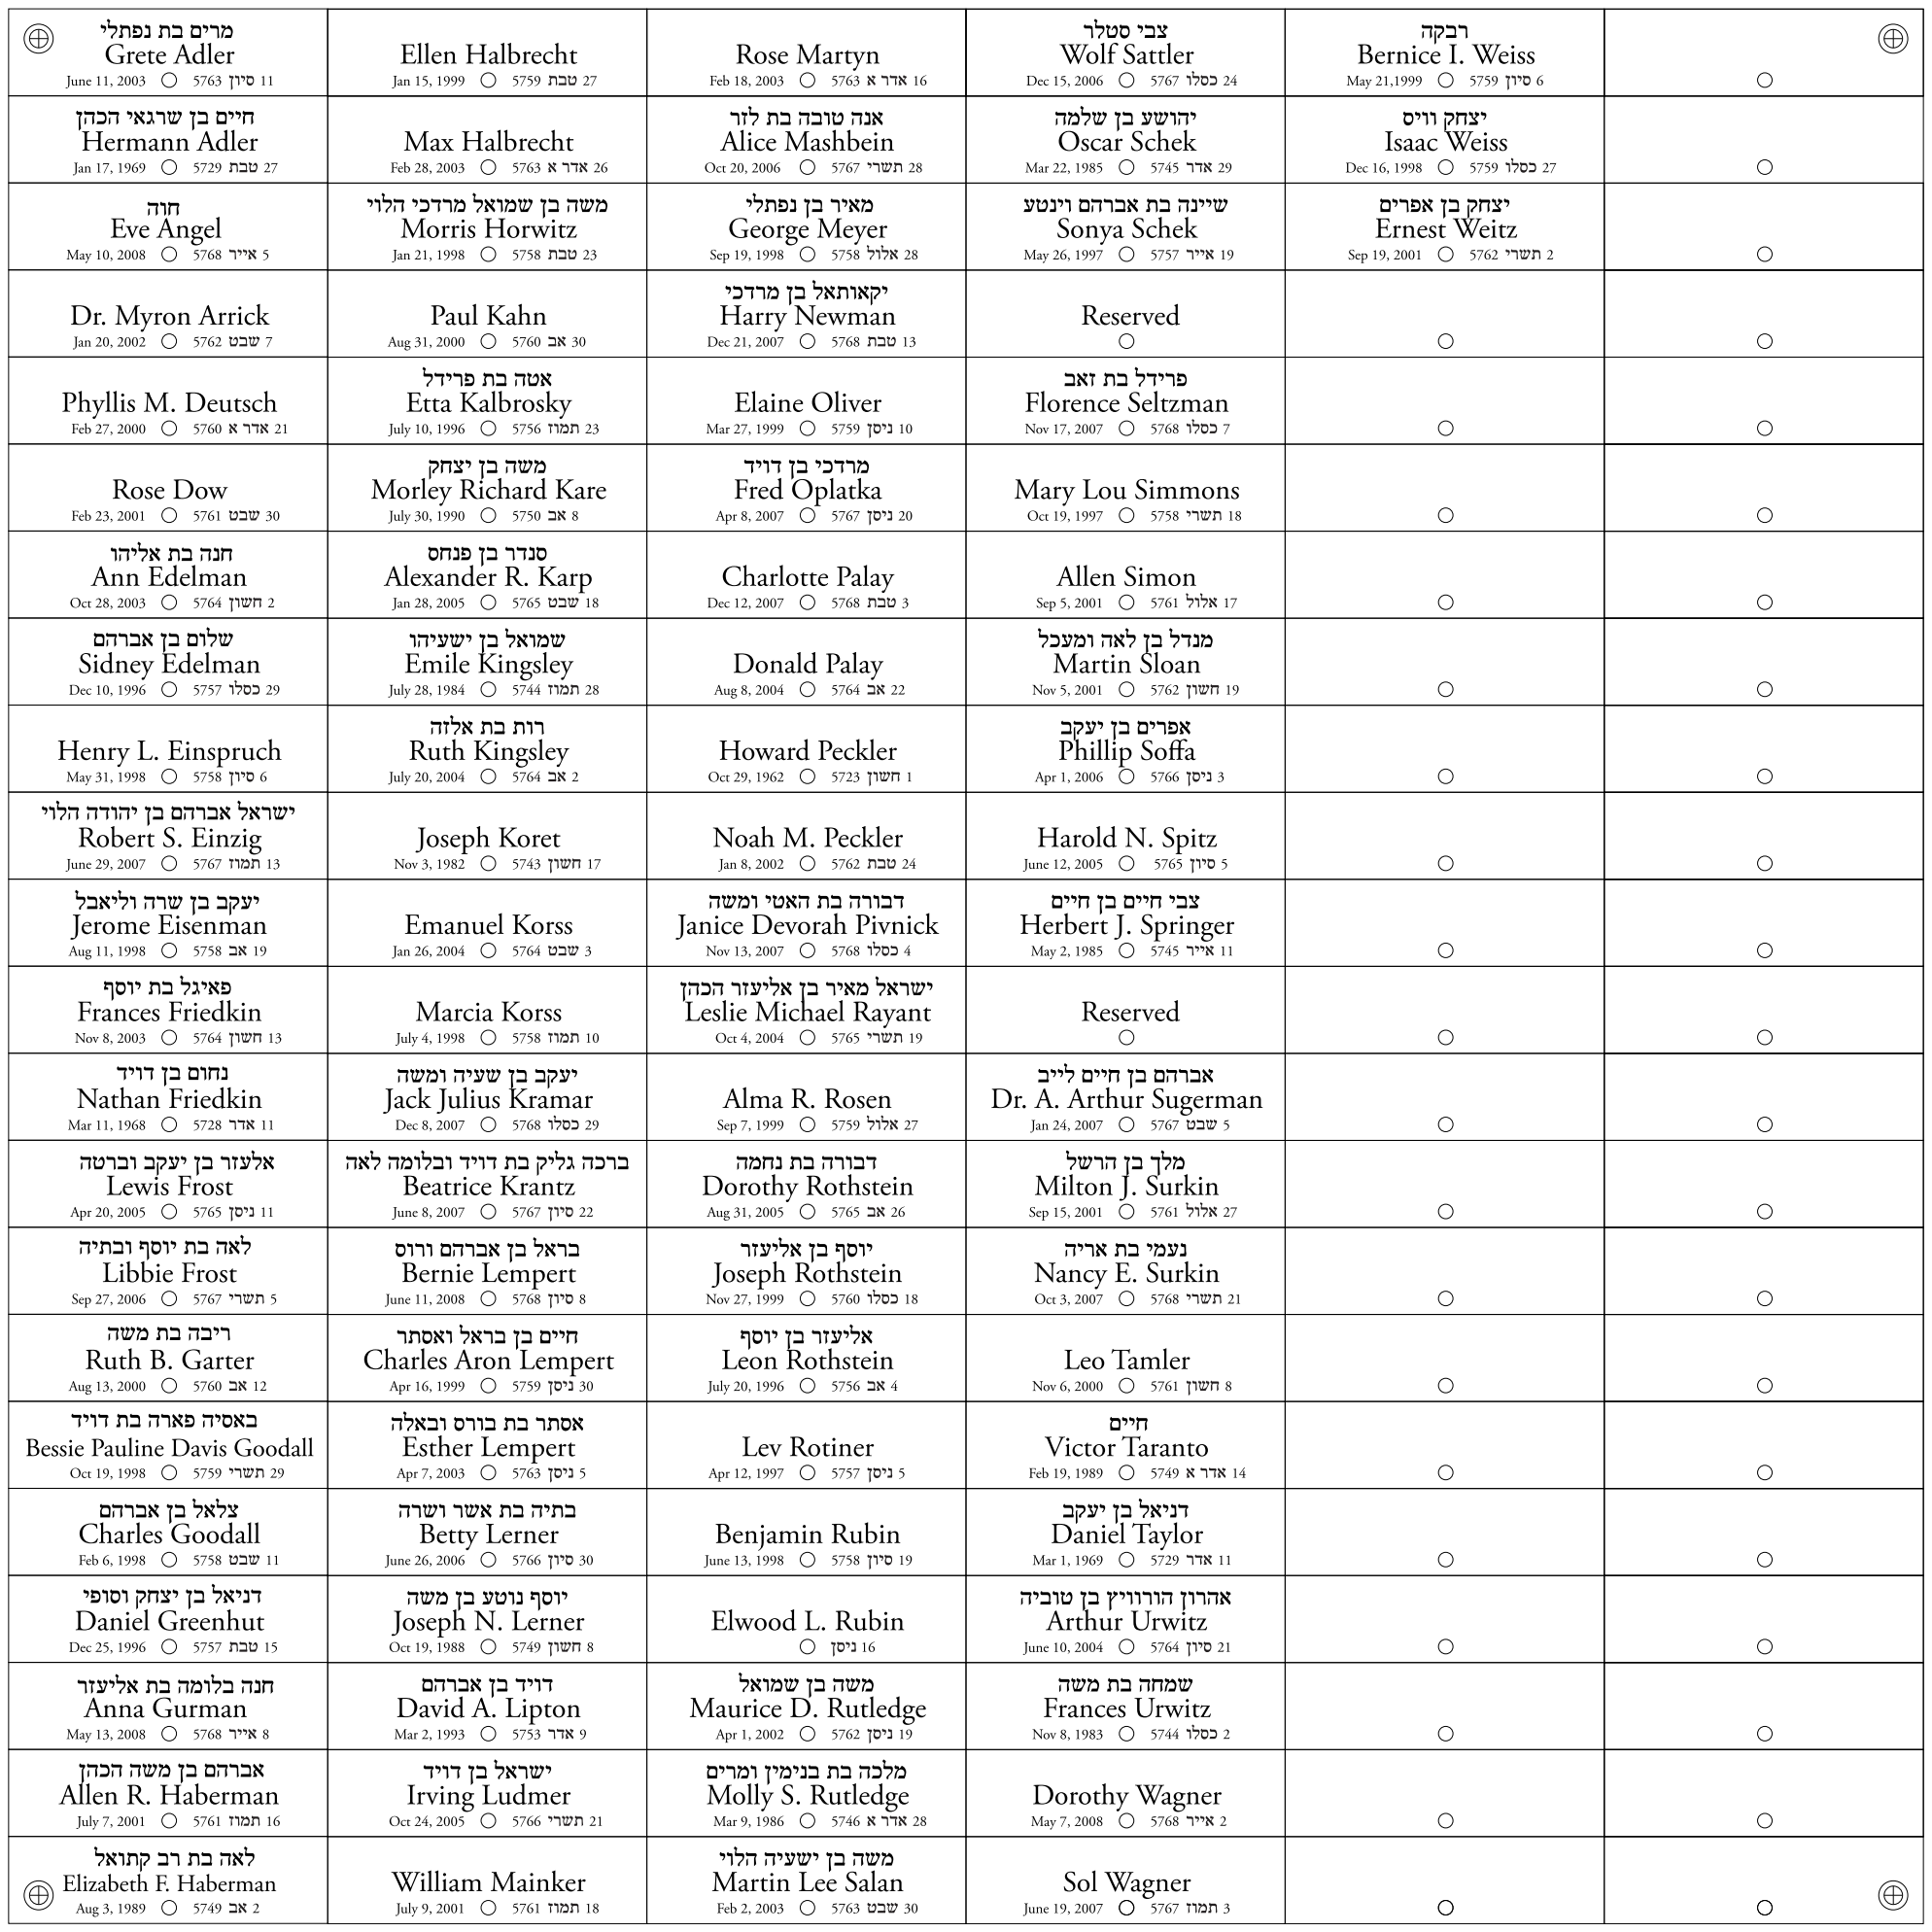
[picture p138: page 1]
