allanschwartz/yahrzeit/panels/panels-2008-08/panel-col3b-noleds.pdf

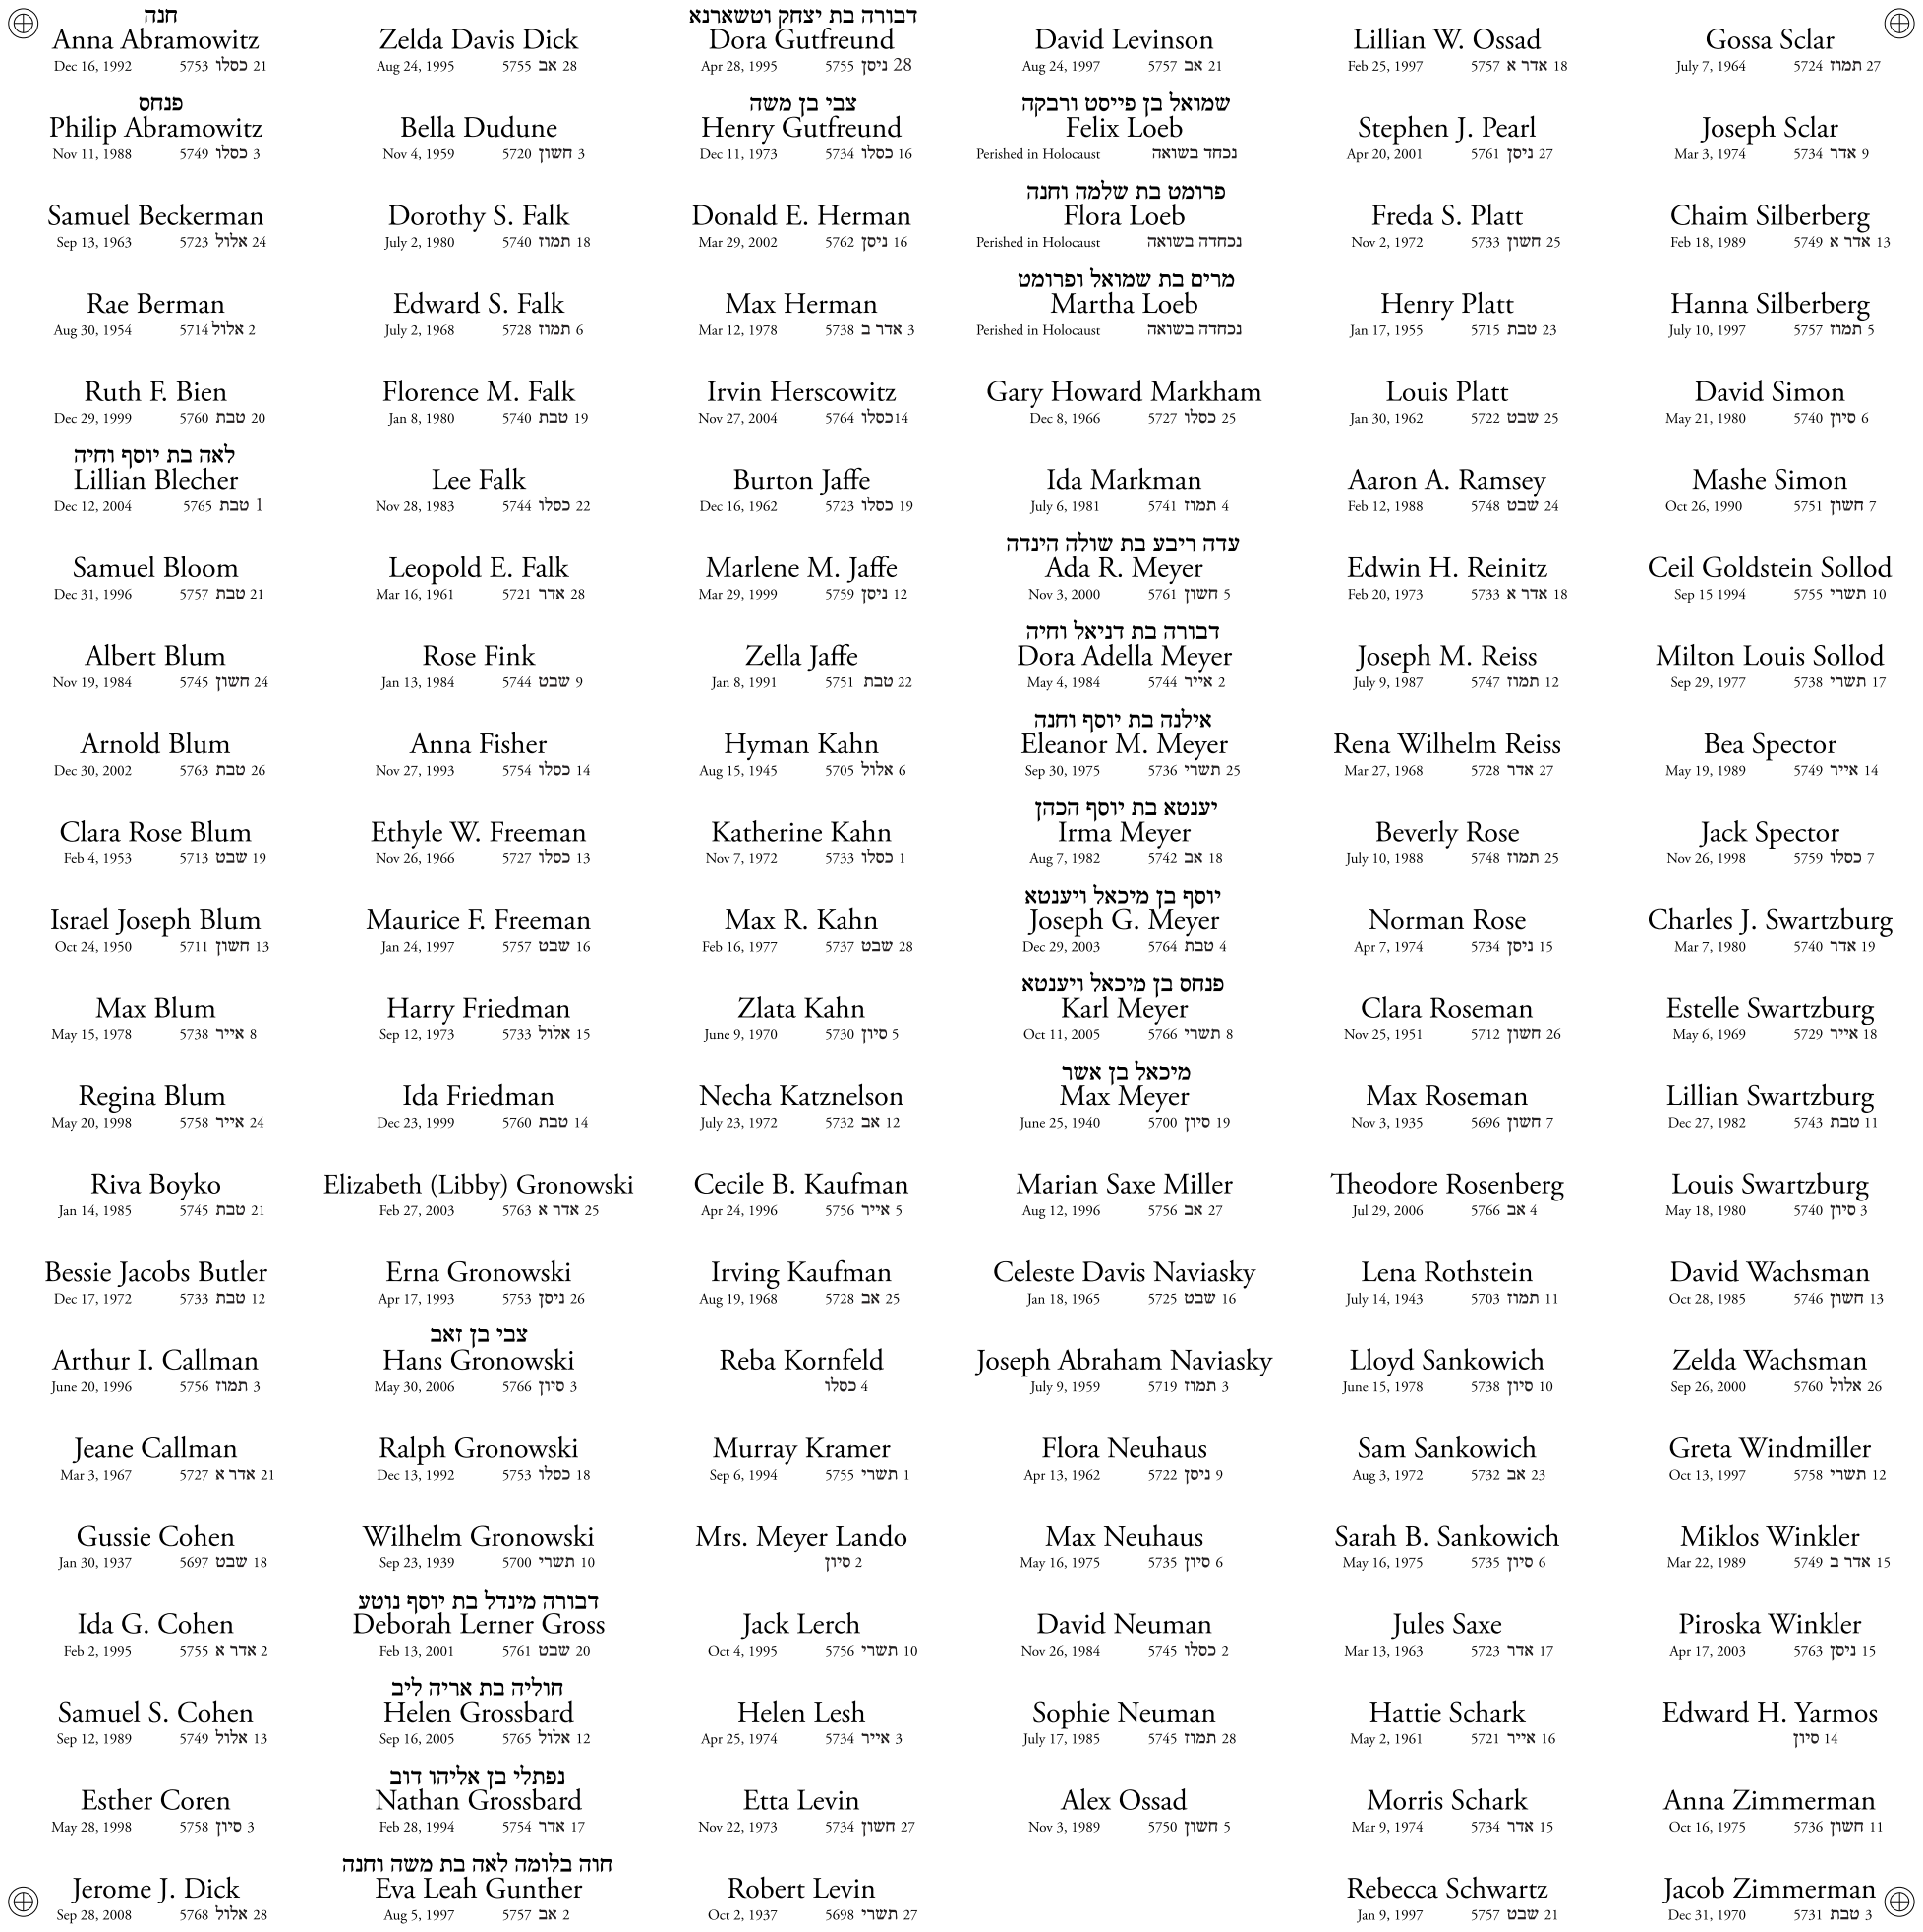
[picture p139: page 1]
