allanschwartz/yahrzeit/panels/panels-2008-08/panel-col3b.pdf

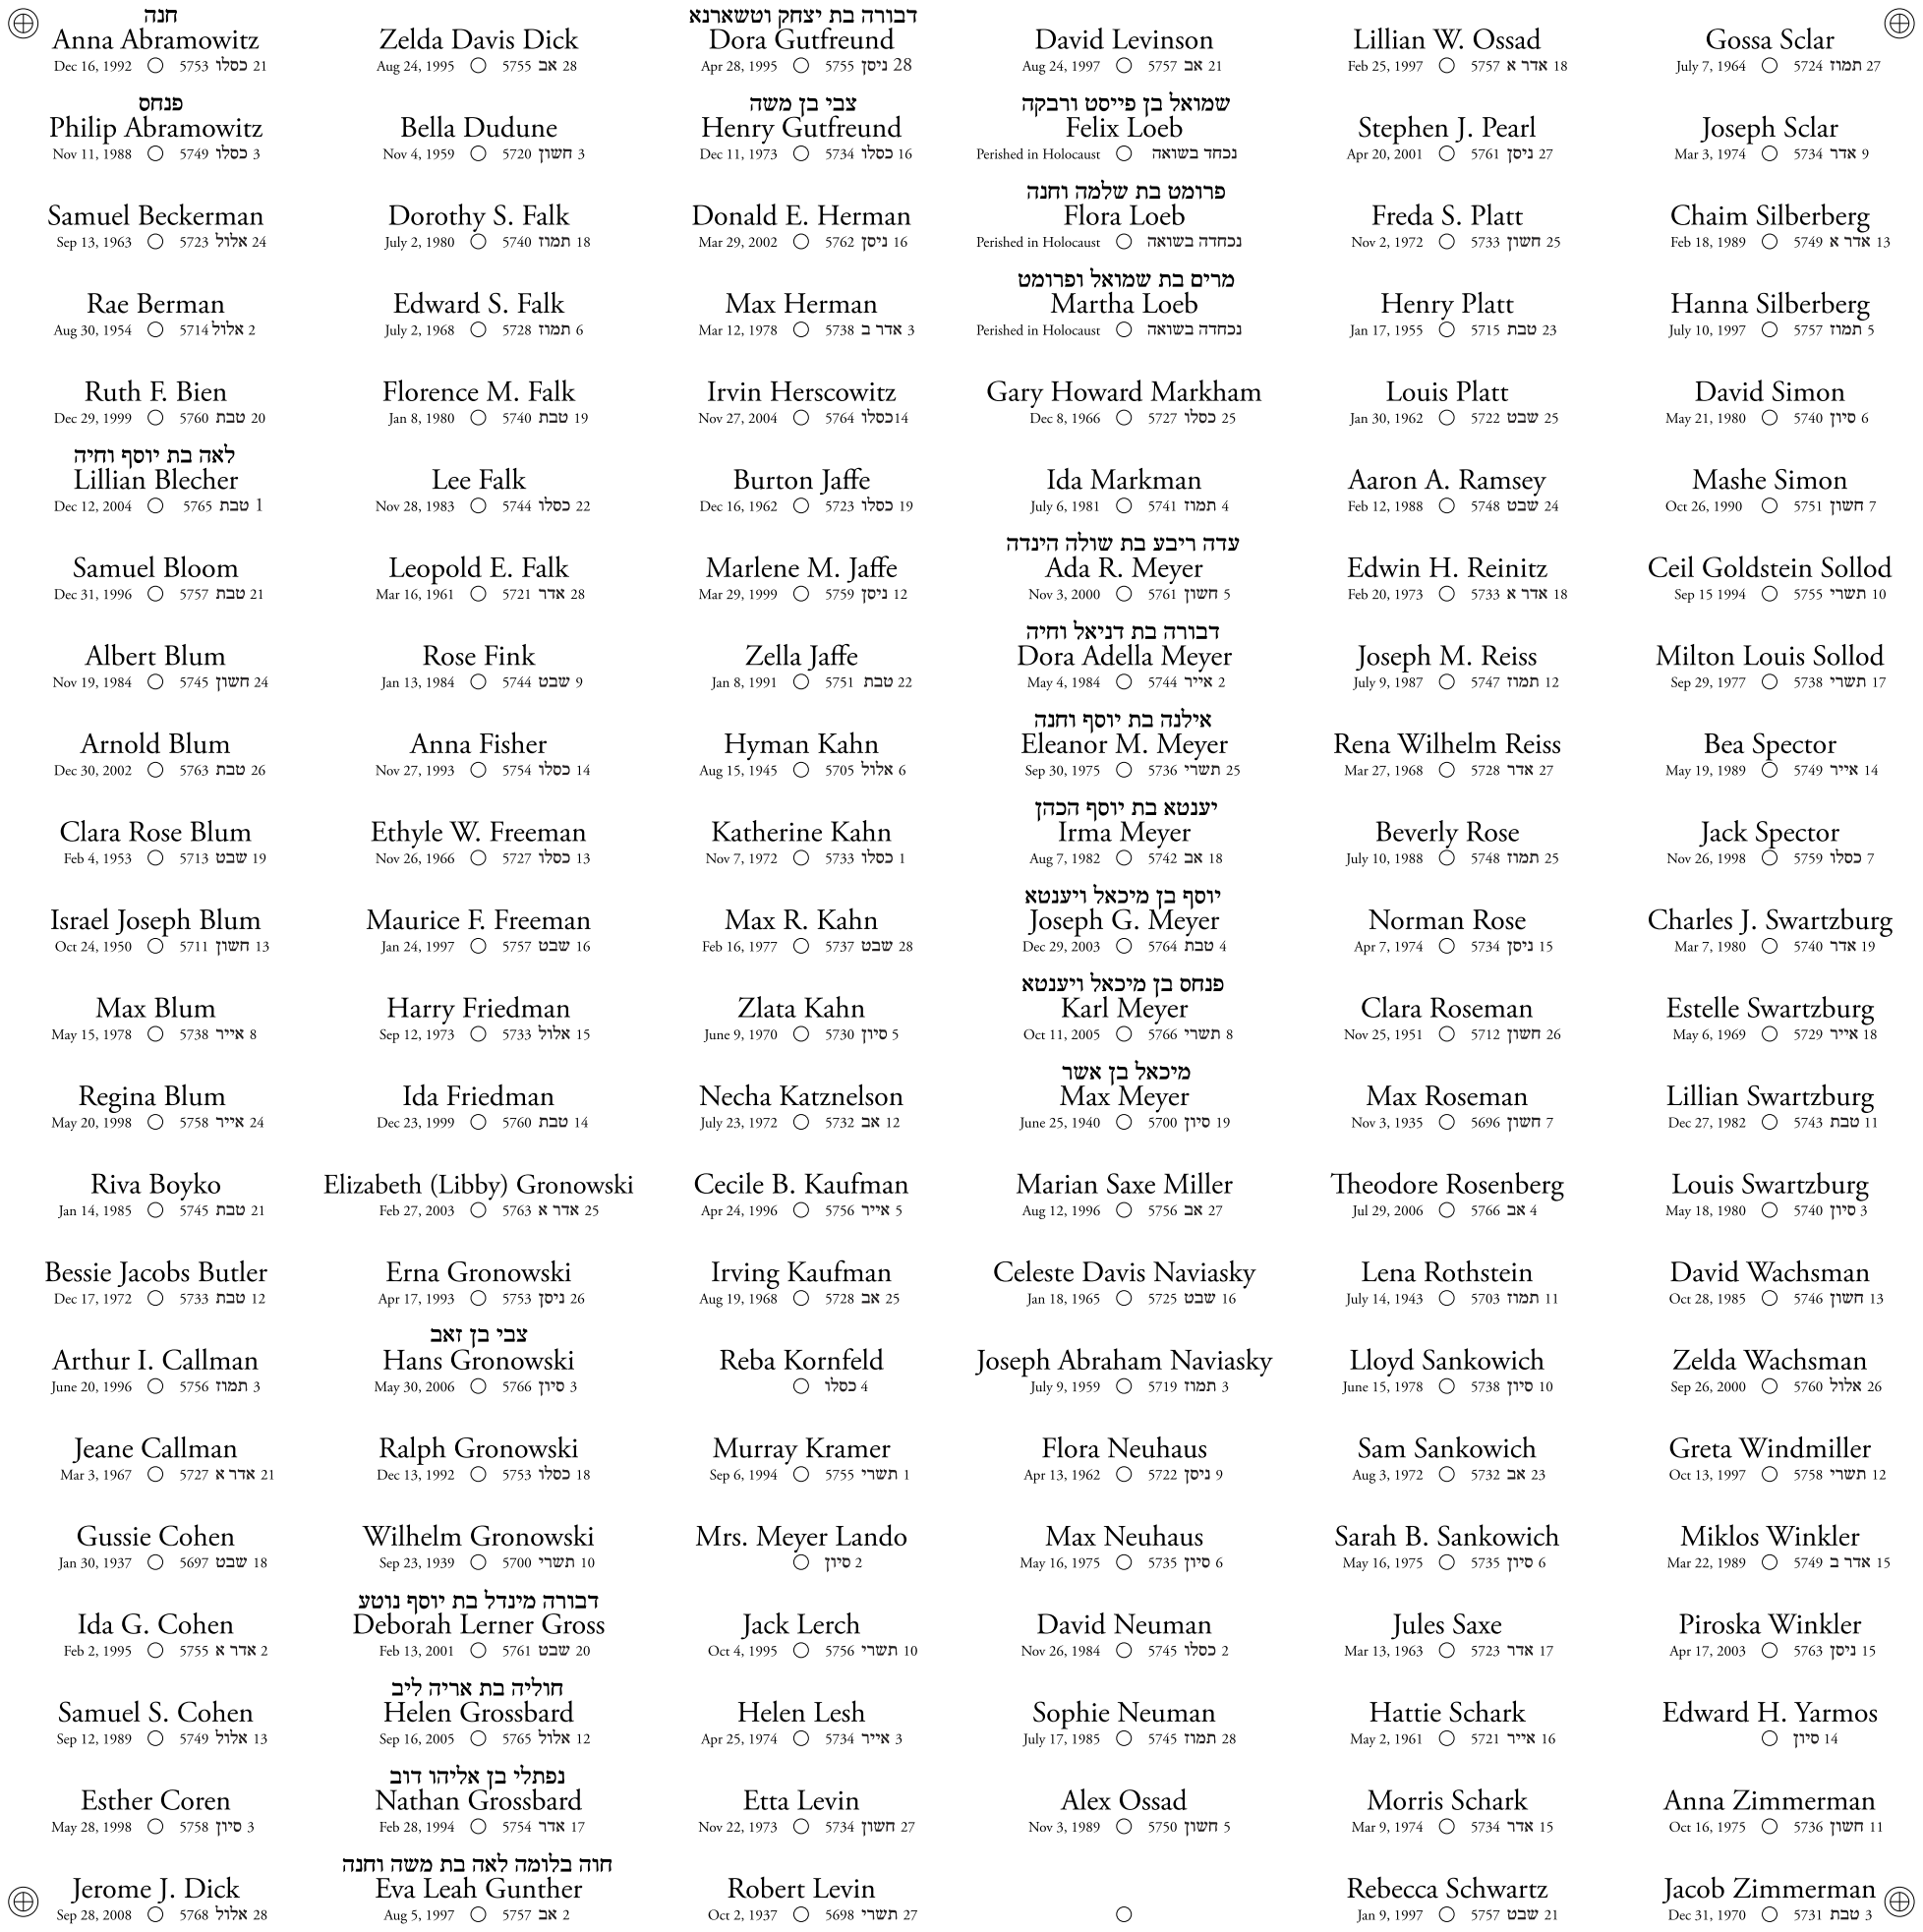
[picture p140: page 1]
