allanschwartz/yahrzeit/panels/panels-2008-08/panel-col3c-noleds.pdf

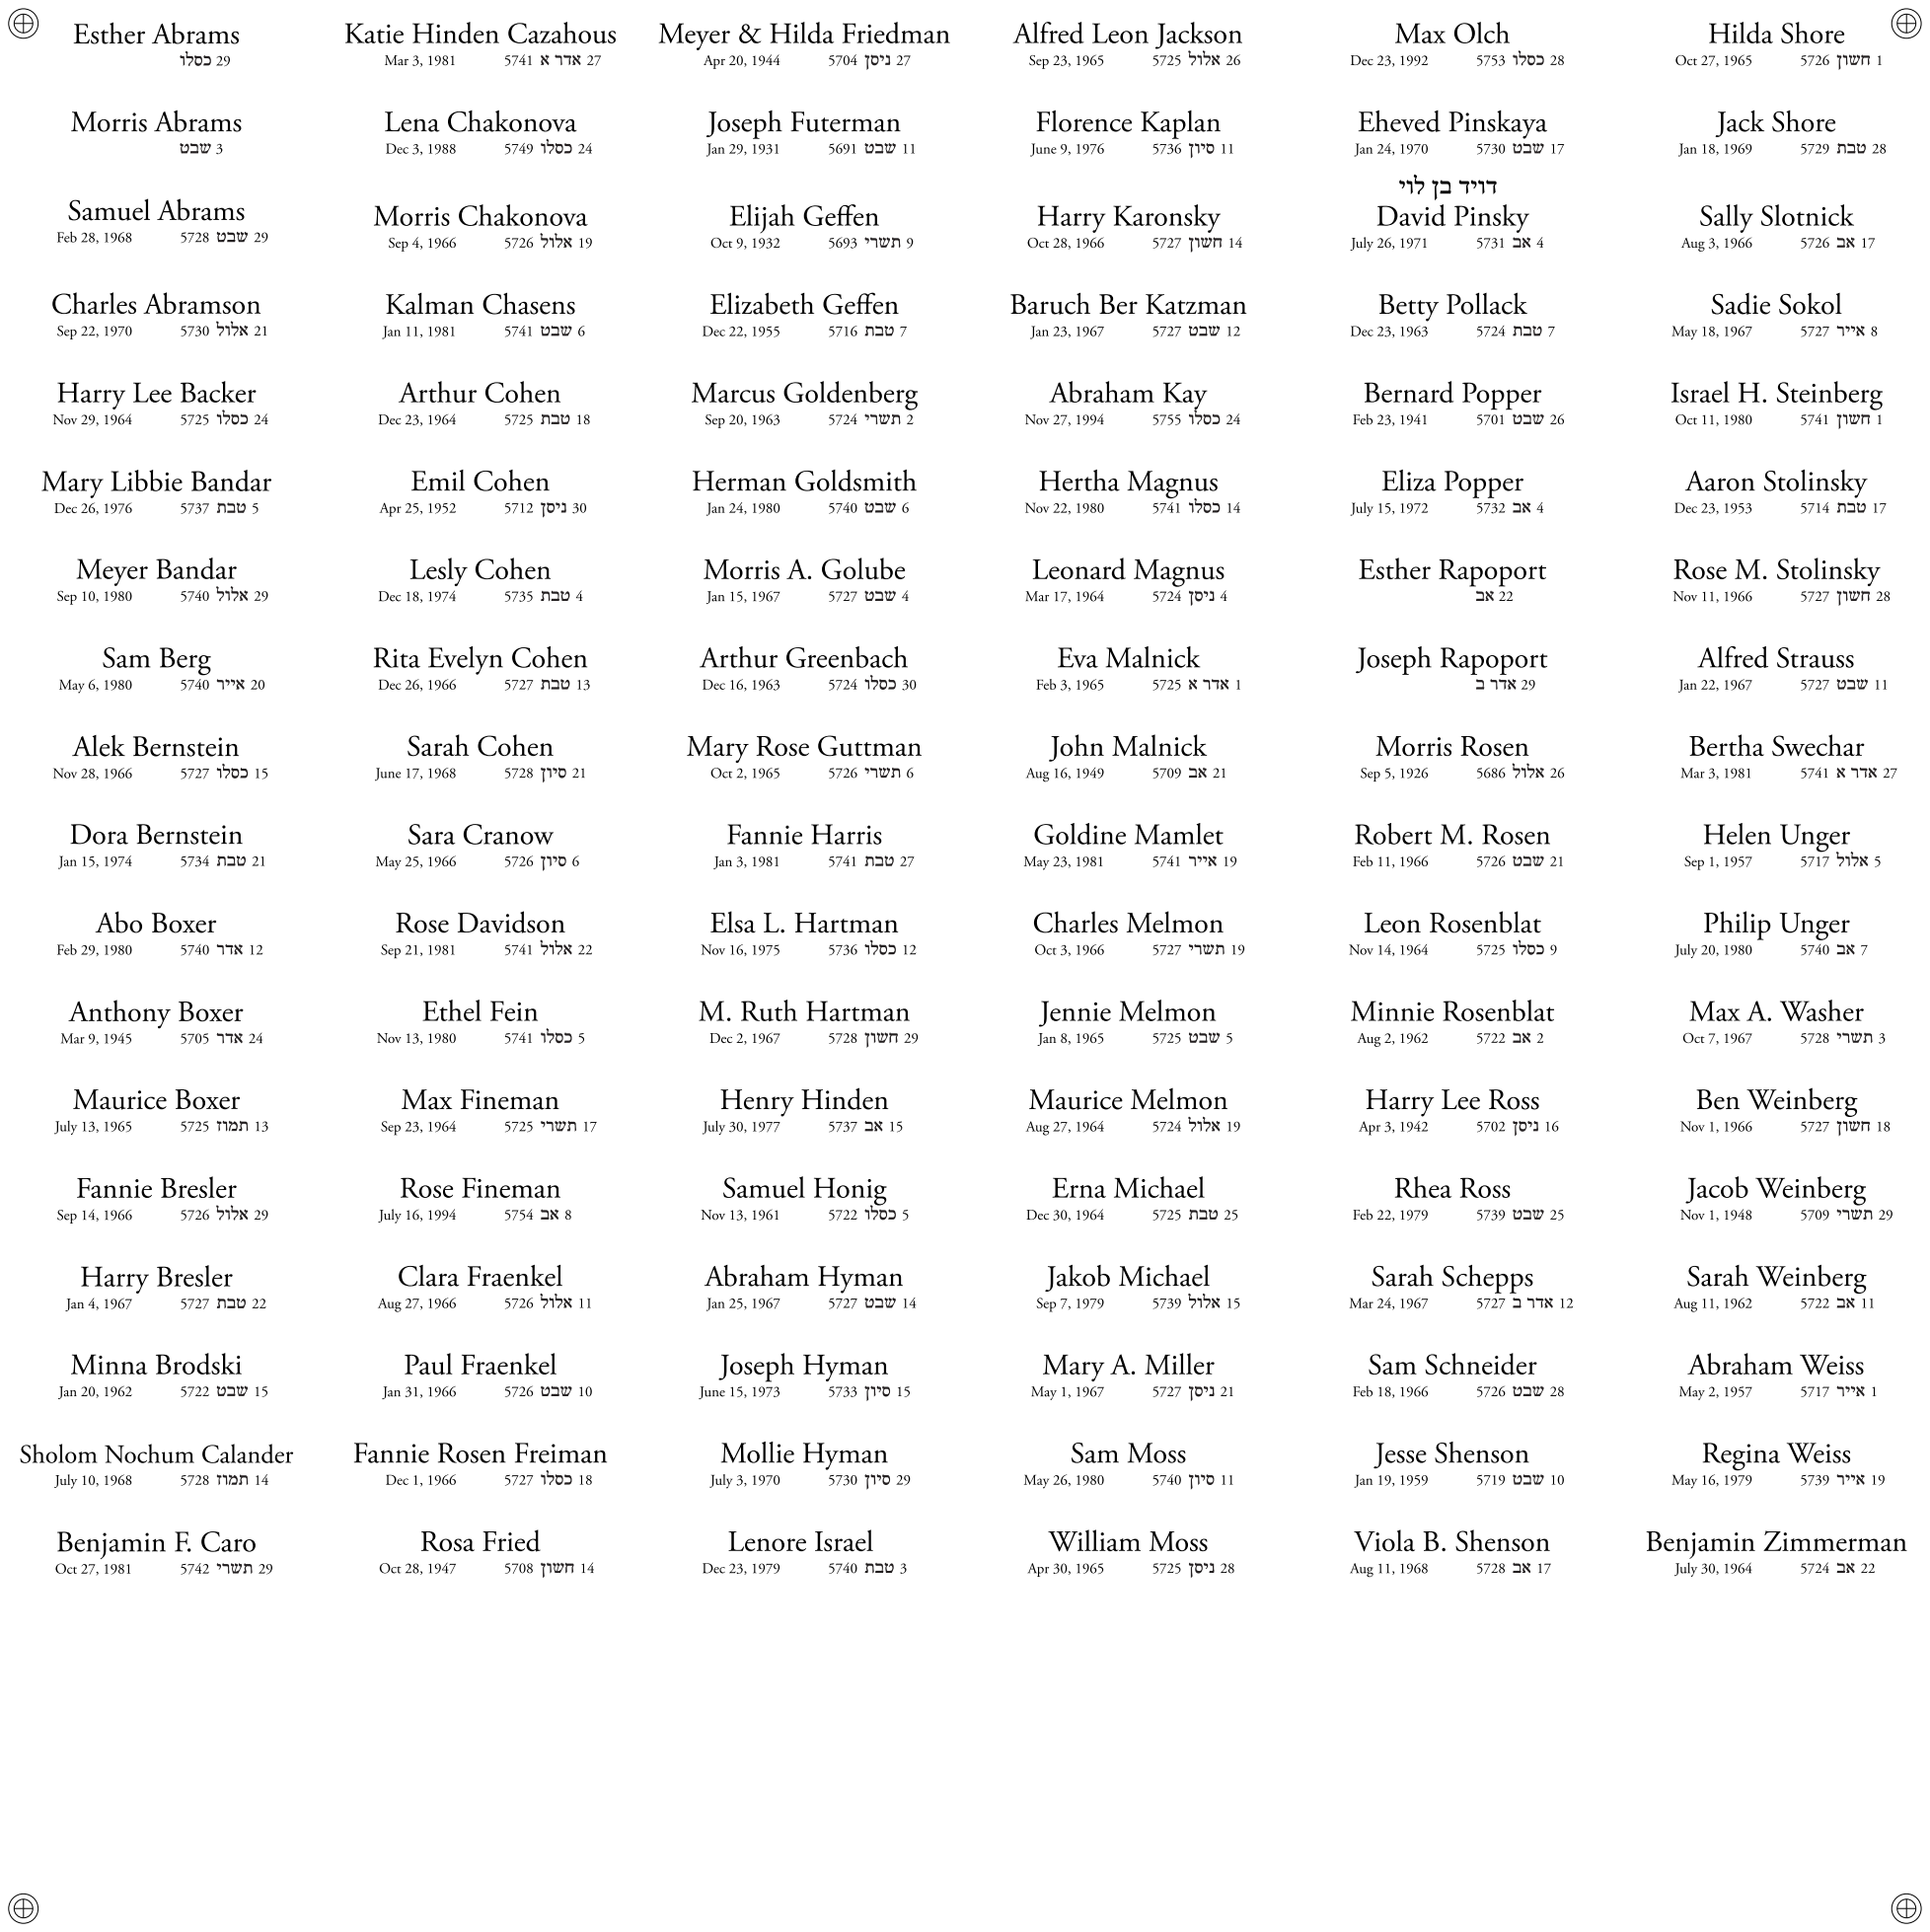
[picture p141: page 1]
