allanschwartz/yahrzeit/panels/panels-2008-08/panel-col3c.pdf

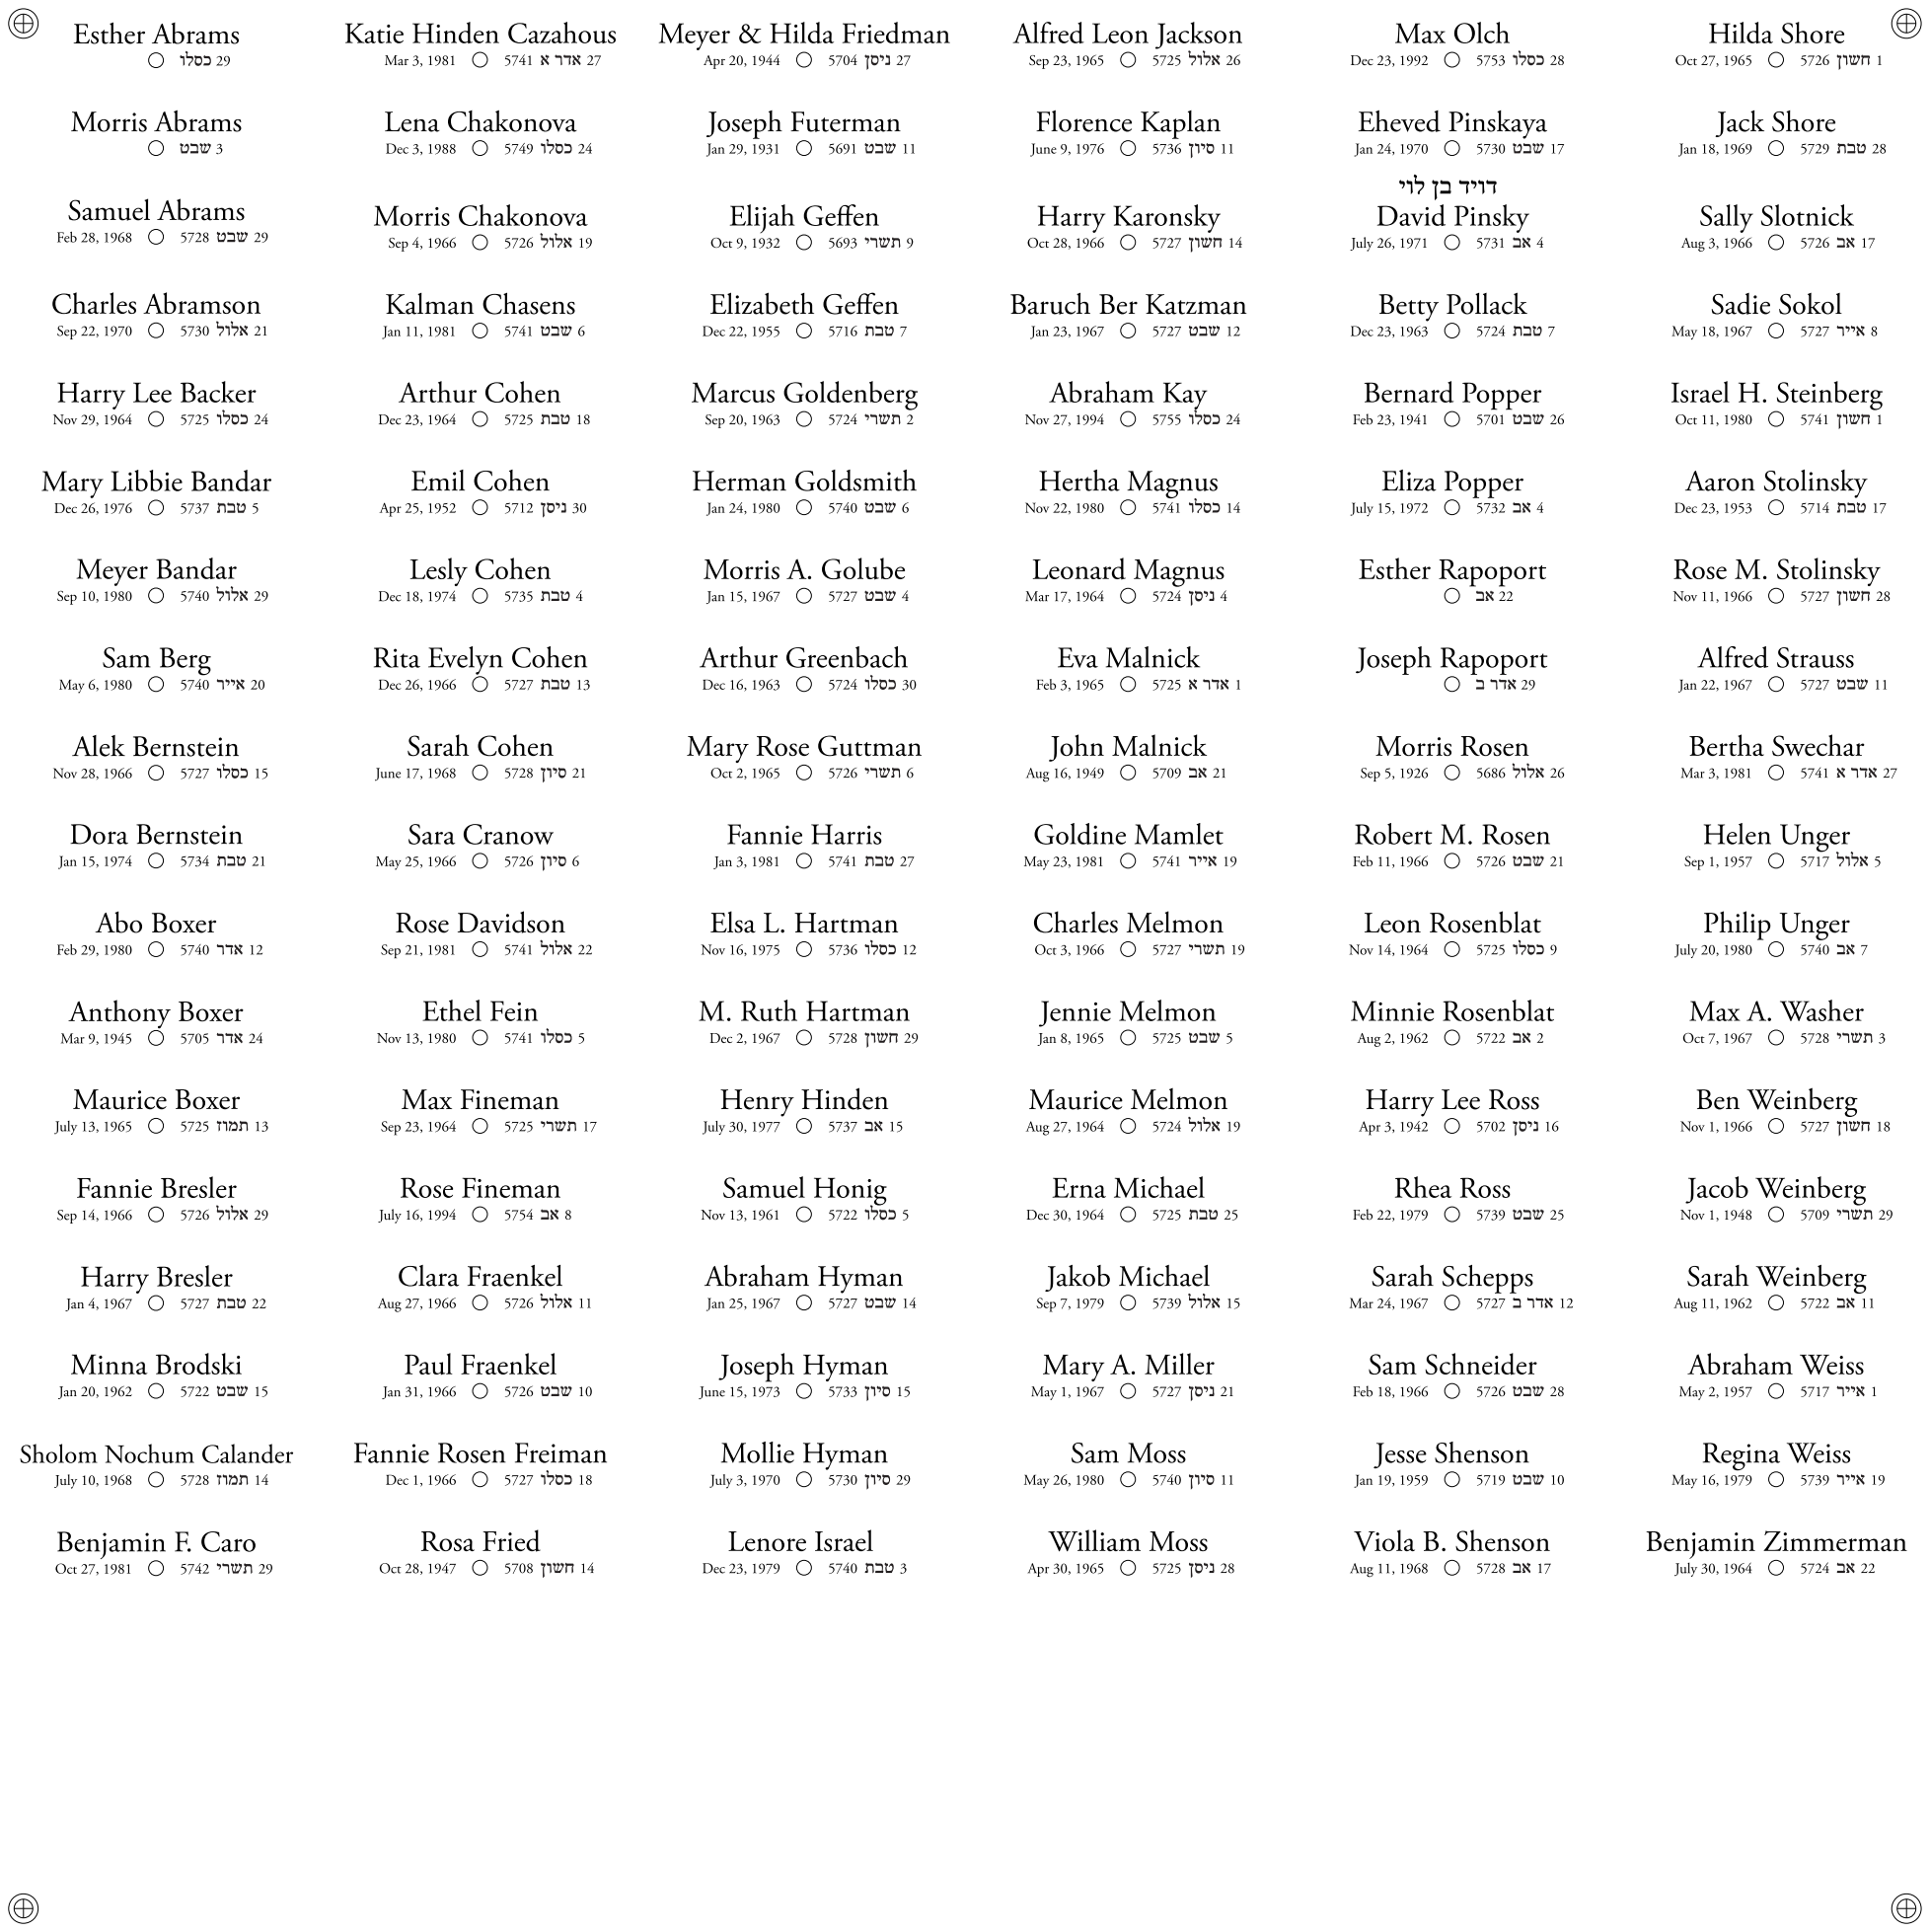
[picture p142: page 1]
