allanschwartz/yahrzeit/panels/panels-2008-08/panel-col5b.pdf

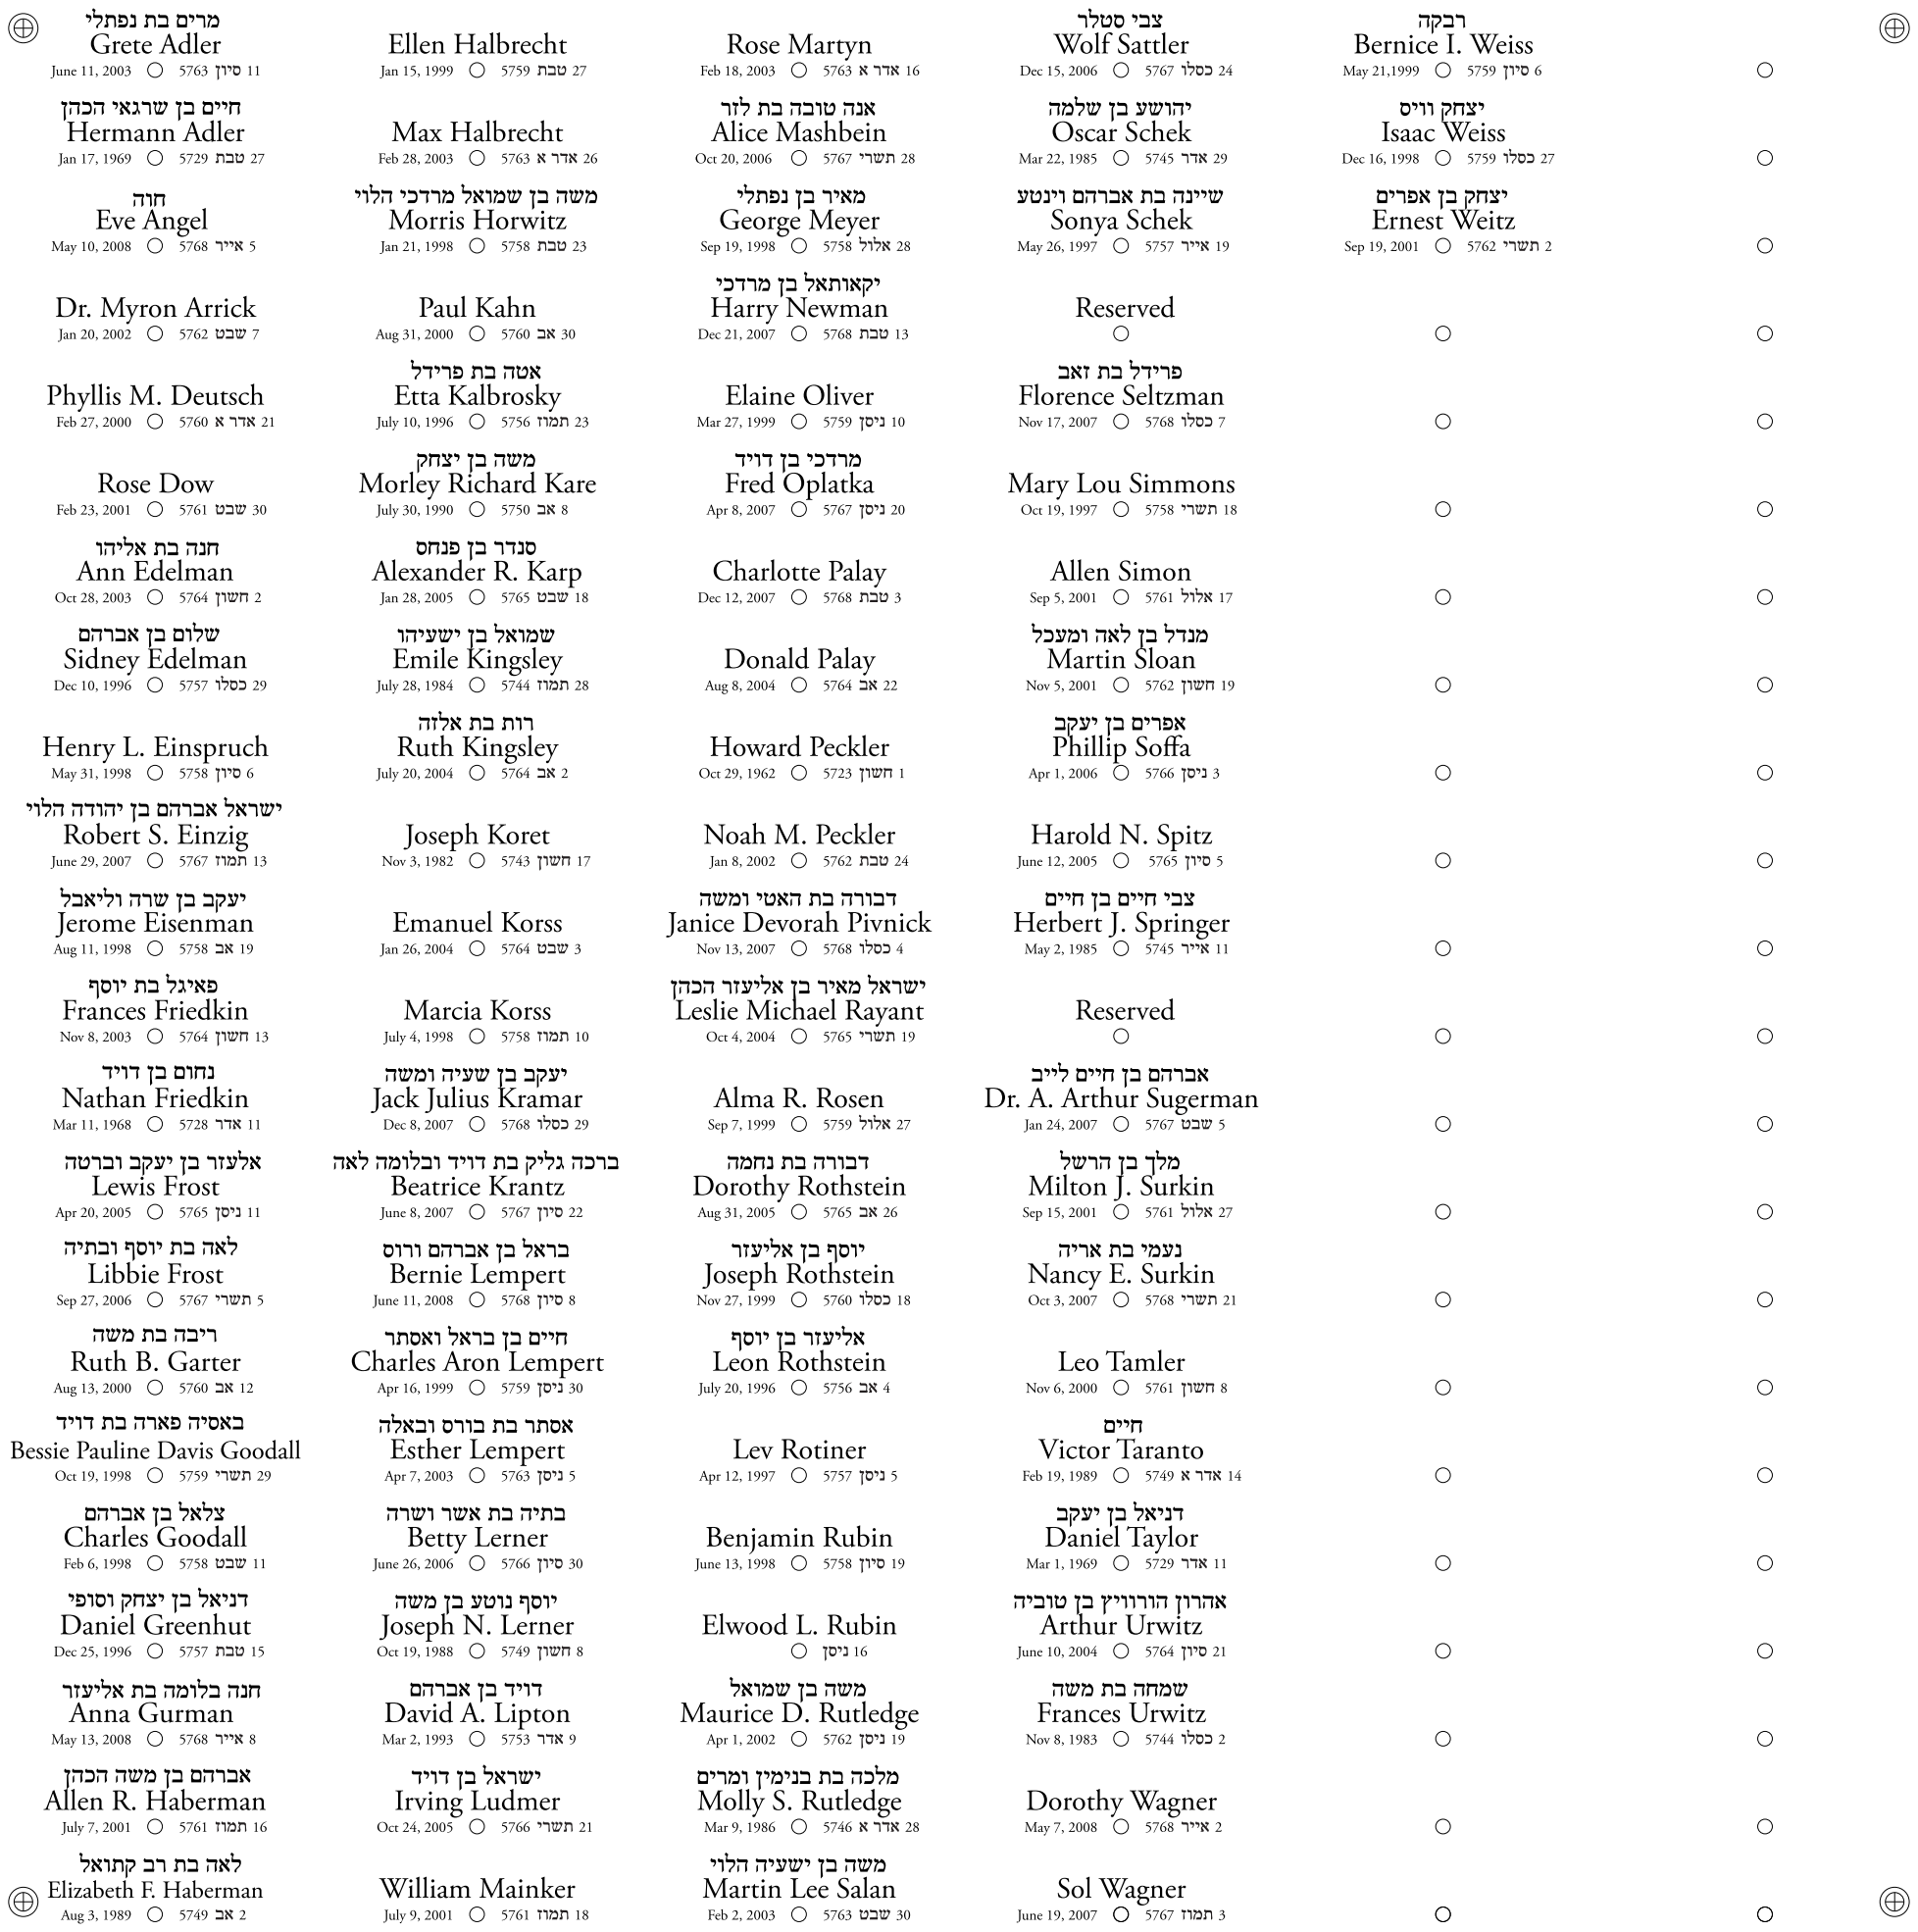
[picture p143: page 1]
