allanschwartz/yahrzeit/panels/panels-2009-05-27/panel-col5a_noleds.pdf

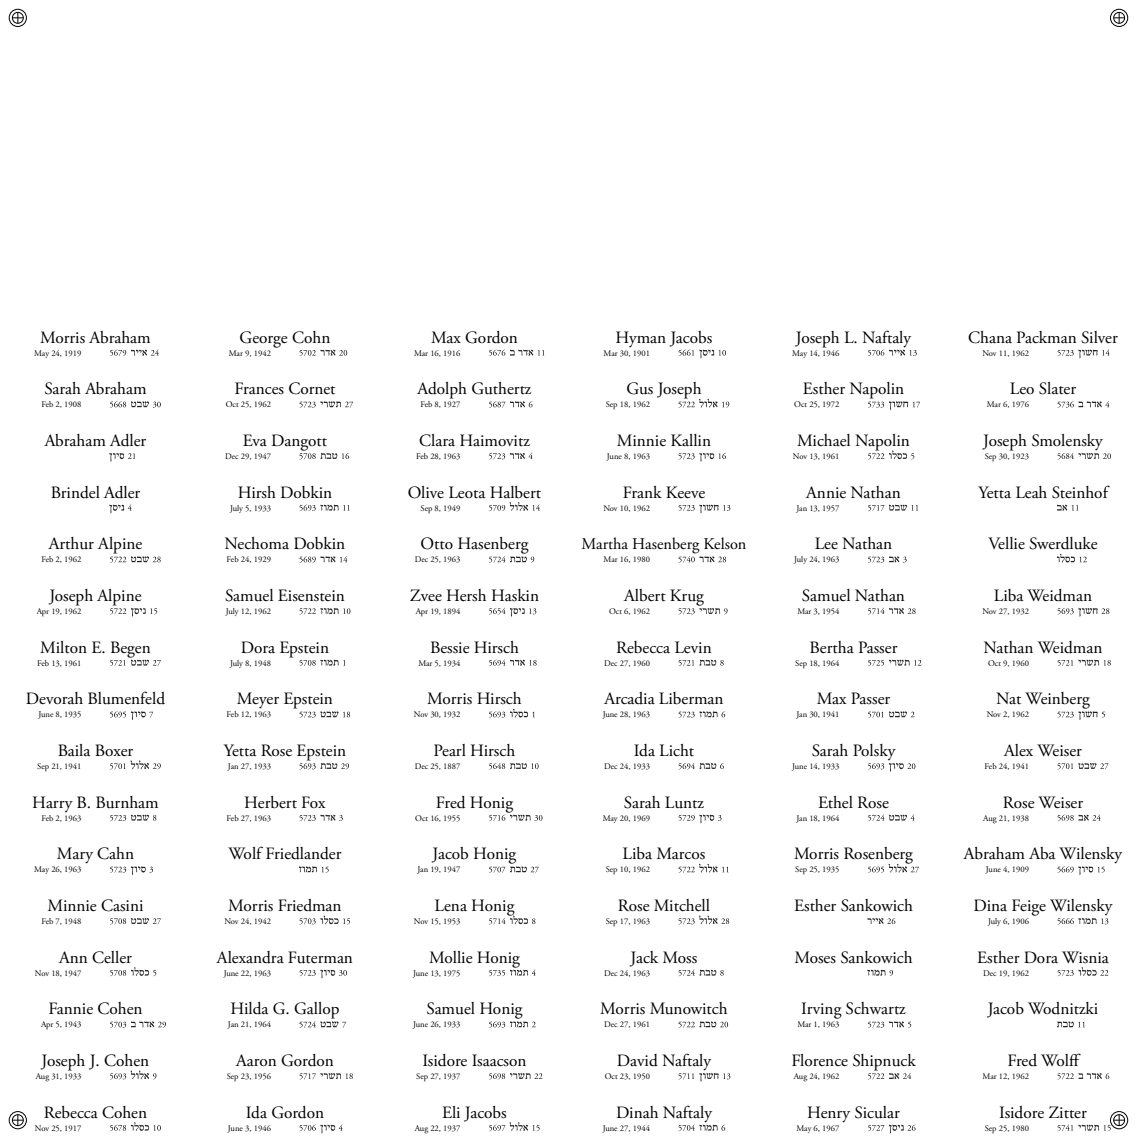
[picture p144: page 1]
Nov 25, 1917; June 3, 1946; Sep 27, 1937; Aug 22, 1937; May 6, 1967; Sep 25, 1980; Sep 23, 1956; June 26, 1933; Aug 24, 1962; Mar 12, 1962; Jan 21, 1964; June 13, 1975; Mar 1, 1963; June 22, 1963; Nov 15, 1953; Dec 19, 1962; Nov 24, 1942; July 6, 1906; Jan 19, 1947; Sep 25, 1935; June 4, 1909; Feb 27, 1963; Oct 16, 1955; Jan 18, 1964; Aug 21, 1938; Jan 27, 1933; Dec 25, 1887; June 14, 1933; Feb 24, 1941; Feb 12, 1963; Nov 30, 1932; Jan 30, 1941; Nov 2, 1962; July 8, 1948; Mar 5, 1934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

drcbh,a vecr vra
Morris Abraham
May 24, 1919
Sarah Abraham
Feb 2, 1908
Abraham Adler

Gus Joseph
Sep 18, 1962
Minnie Kallin
June 8, 1963
Frank Keeve
Nov 10, 1962
Martha Hasenberg Kelson
Mar 16, 1980
Albert Krug
Oct 6, 1962
Rebecca Levin
Dec 27, 1960
Arcadia Liberman
June 28, 1963
Ida Licht
Dec 24, 1933
Sarah Luntz
May 20, 1969
Liba Marcos
Sep 10, 1962
Rose Mitchell
Sep 17, 1963
Jack Moss
Dec 24, 1963
Morris Munowitch
Dec 27, 1961
David Naftaly
Oct 23, 1950
Dinah Naftaly
June 27, 1944

Brindel Adler

Arthur Alpine
Feb 2, 1962
Joseph Alpine
Apr 19, 1962
Milton E. Begen
Feb 13, 1961
Devorah Blumenfeld
June 8, 1935
Baila Boxer
Sep 21, 1941
Harry B. Burnham
Feb 2, 1963
Mary Cahn
May 26, 1963
Minnie Casini
Feb 7, 1948
Ann Celler
Nov 18, 1947
Fannie Cohen
Apr 5, 1943
Joseph J. Cohen
Aug 31, 1933
