allanschwartz/yahrzeit/panels/panels-2009-05-27/panel-col5b_noleds.pdf

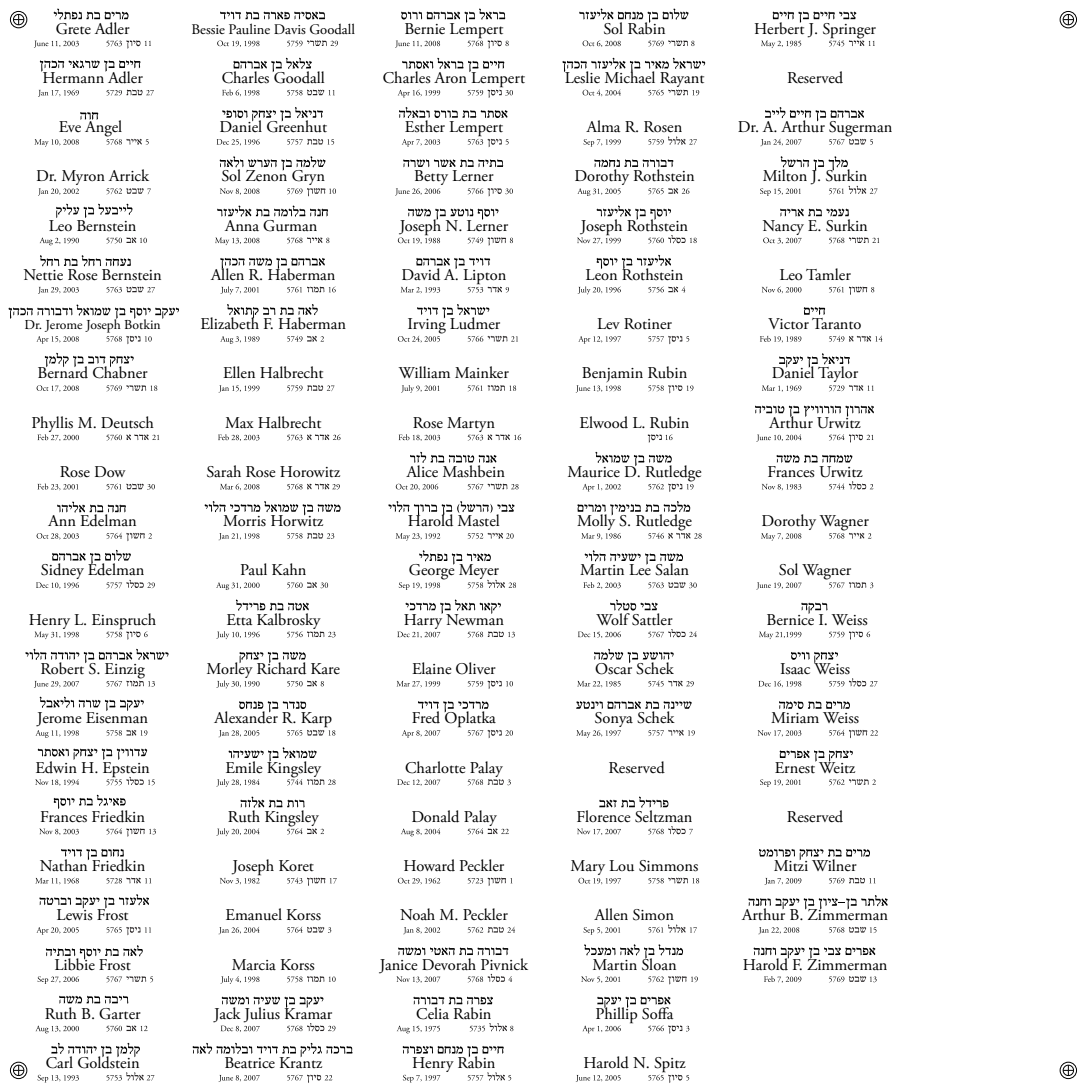
[picture p145: page 1]
Alice Mashbein; Oscar Schek; William Mainker; Irving Ludmer; Molly S. Rutledge; David A. Lipton; Maurice D. Rutledge; Joseph N. Lerner; Elwood L. Rubin; Betty Lerner; Benjamin Rubin; Esther Lempert; Lev Rotiner; Bernie Lempert; Leon Rothstein; Beatrice Krantz; Joseph Rothstein; Dorothy Rothstein; Marcia Korss; Alma R. Rosen; Emanuel Korss; Joseph Koret; Sol Rabin; Reserved; Etta Kalbrosky; Alexander R. Karp; Emile Kingsley; Ruth Kingsley; Henry Rabin; Herbert J. Springer; Paul Kahn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

Bessie Pauline Davis Goodall

Charles Aron Lempert

Leslie Michael Rayant

Dr. A. Arthur Sugerman

Dr. Myron Arrick

Sol Zenon Gryn

Nettie Rose Bernstein

Dr. Jerome Joseph Botkin

Sarah Rose Horowitz

Martin Lee Salan

Morley Richard Kare

Mary Lou Simmons

Janice Devorah Pivnick

Jack Julius Kramar
