allanschwartz/yahrzeit/panels/panels-2009-05-27/panel-col6a_20090527-a.pdf

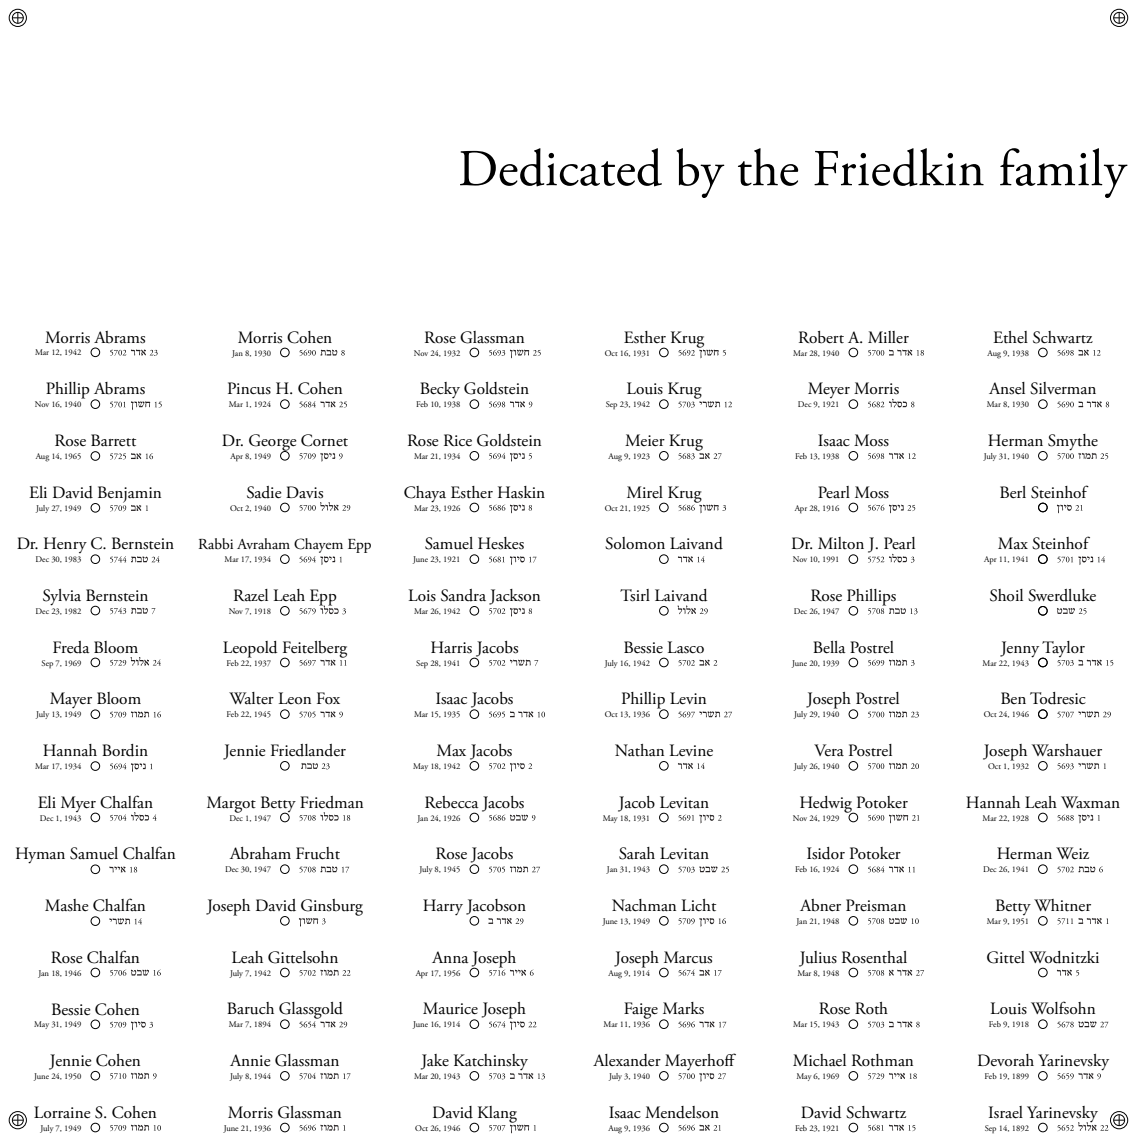
[picture p146: page 1]
Jan 18, 1946; May 31, 1949; June 24, 1950; July 7, 1949; June 21, 1936; Oct 26, 1946; Aug 9, 1936; Feb 23, 1921; Sep 14, 1892; July 8, 1944; Mar 20, 1943; July 3, 1940; May 6, 1969; Feb 19, 1899; Mar 7, 1894; June 16, 1914; Mar 11, 1936; Mar 15, 1943; Feb 9, 1918; July 7, 1942; Apr 17, 1956; Aug 9, 1914; Mar 8, 1948; June 13, 1949; Jan 21, 1948; Mar 9, 1951; Dec 30, 1947; July 8, 1945; Jan 31, 1943; Feb 16, 1924; Dec 26, 1941; Dec 1, 1947; Jan 24, 1926; May 18, 1931; Nov 24, 1929; Mar 22, 1928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

Morris Abrams
Mar 12, 1942
Phillip Abrams
Nov 16, 1940
Rose Barrett
Aug 14, 1965
Eli David Benjamin
July 27, 1949
Dr. Henry C. Bernstein
Dec 30, 1983
Sylvia Bernstein
Dec 23, 1982
Freda Bloom
Sep 7, 1969
Mayer Bloom
July 13, 1949
Hannah Bordin
Mar 17, 1934
Eli Myer Chalfan
Dec 1, 1943
Hyman Samuel Chalfan
