allanschwartz/yahrzeit/panels/panels-2009-05-27/panel-col6a_noleds-d.pdf

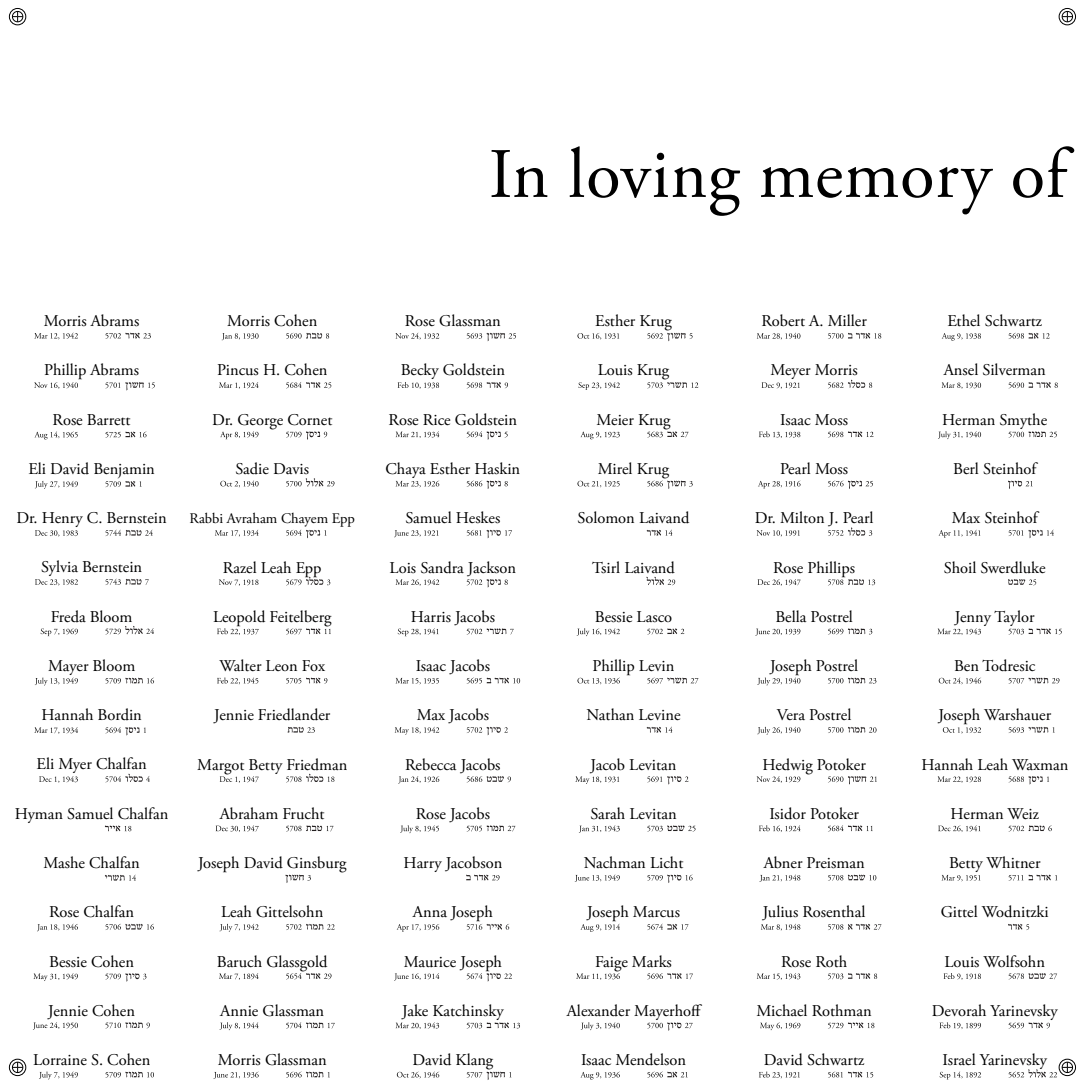
[picture p147: page 1]
Phillip Abrams; Rose Barrett; Sylvia Bernstein; Mayer Bloom; Hannah Bordin; Mashe Chalfan; Rose Chalfan; Bessie Cohen; Jennie Cohen; Lorraine S. Cohen; Morris Glassman; David Klang; Isaac Mendelson; David Schwartz; Israel Yarinevsky; Annie Glassman; Jake Katchinsky; Alexander Mayerhoff; Michael Rothman; Devorah Yarinevsky; Baruch Glassgold; Maurice Joseph; Faige Marks; Rose Roth; Louis Wolfsohn; Leah Gittelsohn; Anna Joseph; Joseph Marcus; Julius Rosenthal; Gittel Wodnitzki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

Eli David Benjamin

Dr. Henry C. Bernstein

Eli Myer Chalfan

Hyman Samuel Chalfan
