allanschwartz/yahrzeit/panels/panels-2009-05-27/panel-col7a_20090527-a.pdf

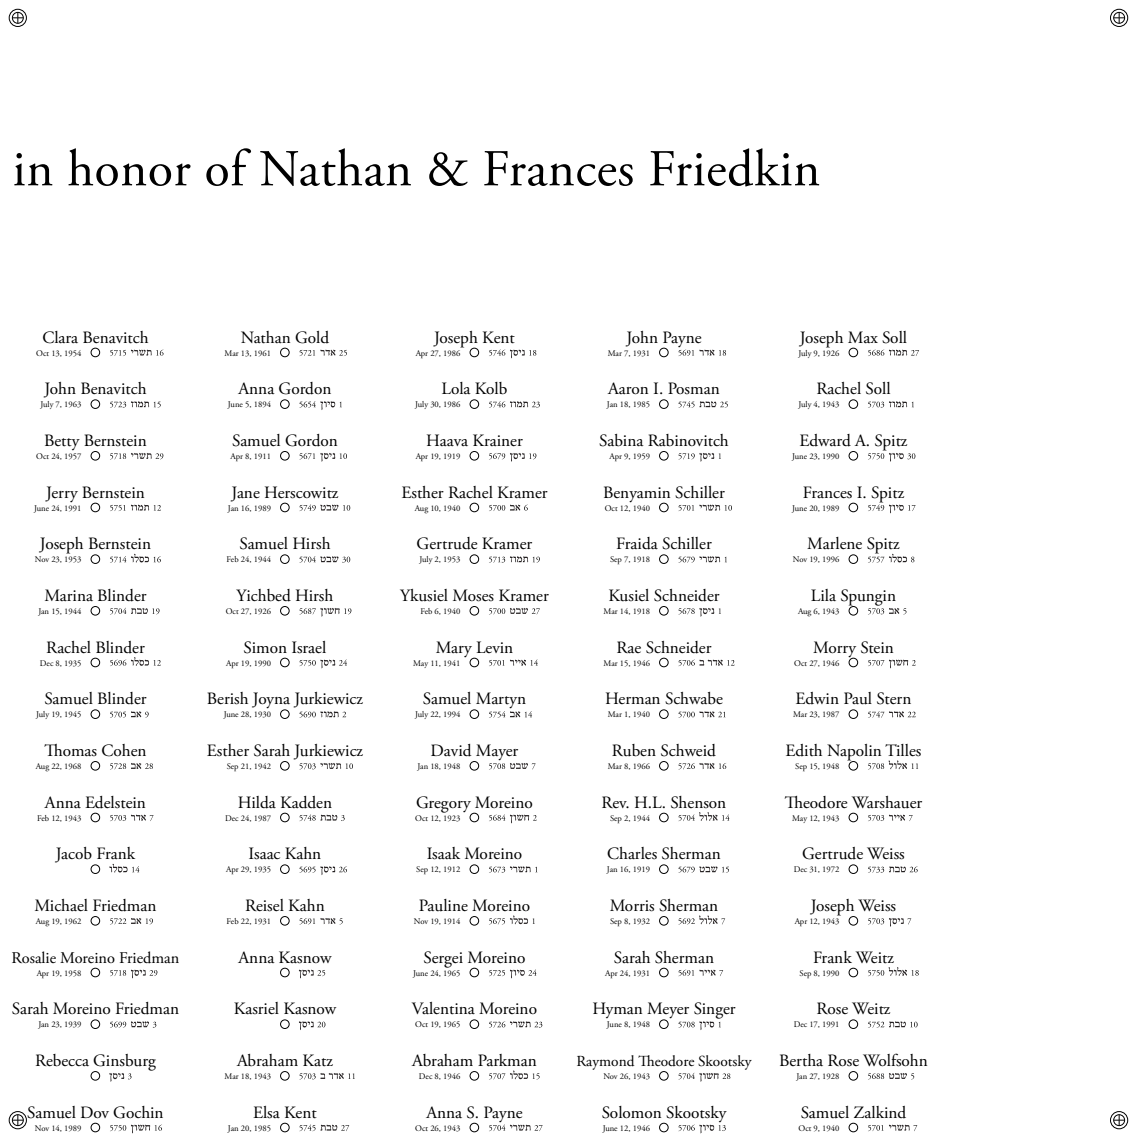
[picture p148: page 1]
Oct 13, 1954; July 7, 1963; Oct 24, 1957; June 24, 1991; Nov 23, 1953; Jan 15, 1944; Dec 8, 1935; July 19, 1945; Aug 22, 1968; Feb 12, 1943; Nov 14, 1989; Jan 20, 1985; Oct 26, 1943; June 12, 1946; Oct 9, 1940; Mar 18, 1943; Dec 8, 1946; Nov 26, 1943; Jan 27, 1928; Oct 19, 1965; June 8, 1948; Dec 17, 1991; June 24, 1965; Apr 24, 1931; Sep 8, 1990; Feb 22, 1931; Nov 19, 1914; Sep 8, 1932; Apr 12, 1943; Apr 29, 1935; Sep 12, 1912; Jan 16, 1919; Dec 31, 1972; Dec 24, 1987; Oct 12, 1923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

Michael Friedman
Aug 19, 1962
Rosalie Moreino Friedman
Apr 19, 1958
Sarah Moreino Friedman
Jan 23, 1939
Rebecca Ginsburg
