allanschwartz/yahrzeit/panels/panels-2009-05-27/panel-col7a_20090527-d.pdf

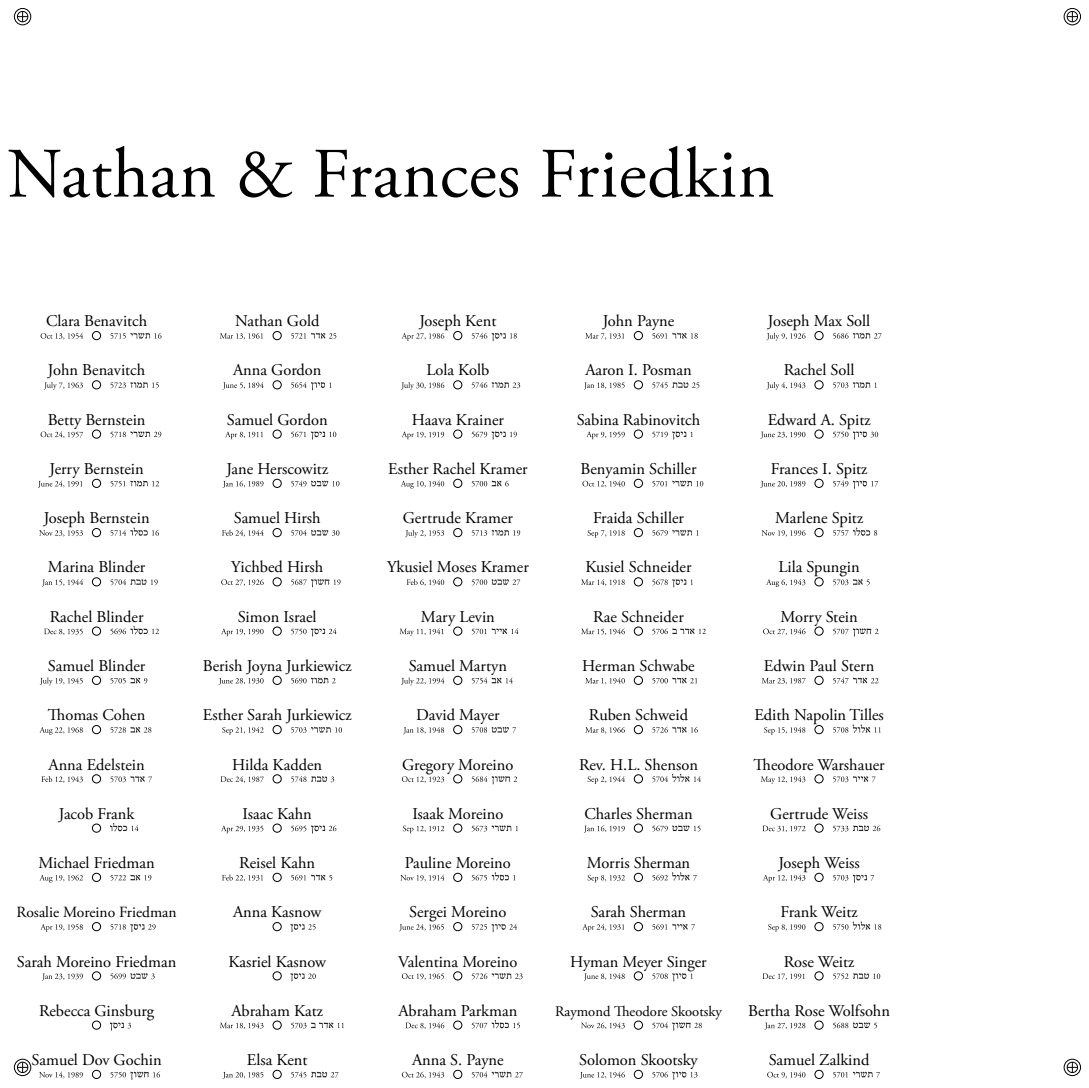
[picture p149: page 1]
drcbh,a vecr vra; Samuel Dov Gochin; Elsa Kent; Anna S. Payne; Solomon Skootsky; Samuel Zalkind; Abraham Katz; Abraham Parkman; Raymond eodore Skootsky; Bertha Rose Wolfsohn; Kasriel Kasnow; Valentina Moreino; Hyman Meyer Singer; Rose Weitz; Anna Kasnow; Sergei Moreino; Sarah Sherman; Frank Weitz; Reisel Kahn; Pauline Moreino; Morris Sherman; Joseph Weiss; Isaac Kahn; Isaak Moreino; Charles Sherman; Gertrude Weiss; Hilda Kadden; Gregory Moreino; Rev. H.L. Shenson; eodore Warshauer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

drcbh,a vecr vra
John Benavitch

Betty Bernstein

Jerry Bernstein

Joseph Bernstein

Marina Blinder

Rachel Blinder

Samuel Blinder

omas Cohen

Anna Edelstein

Jacob Frank

Michael Friedman

Rosalie Moreino Friedman

Sarah Moreino Friedman

Rebecca Ginsburg
