allanschwartz/yahrzeit/Hardware/cables/YYZ Pixel V2 Legacy Power Adapter 01.pdf

## YYZ Pixel V2 Legacy Power Adapter 01

### Diagram

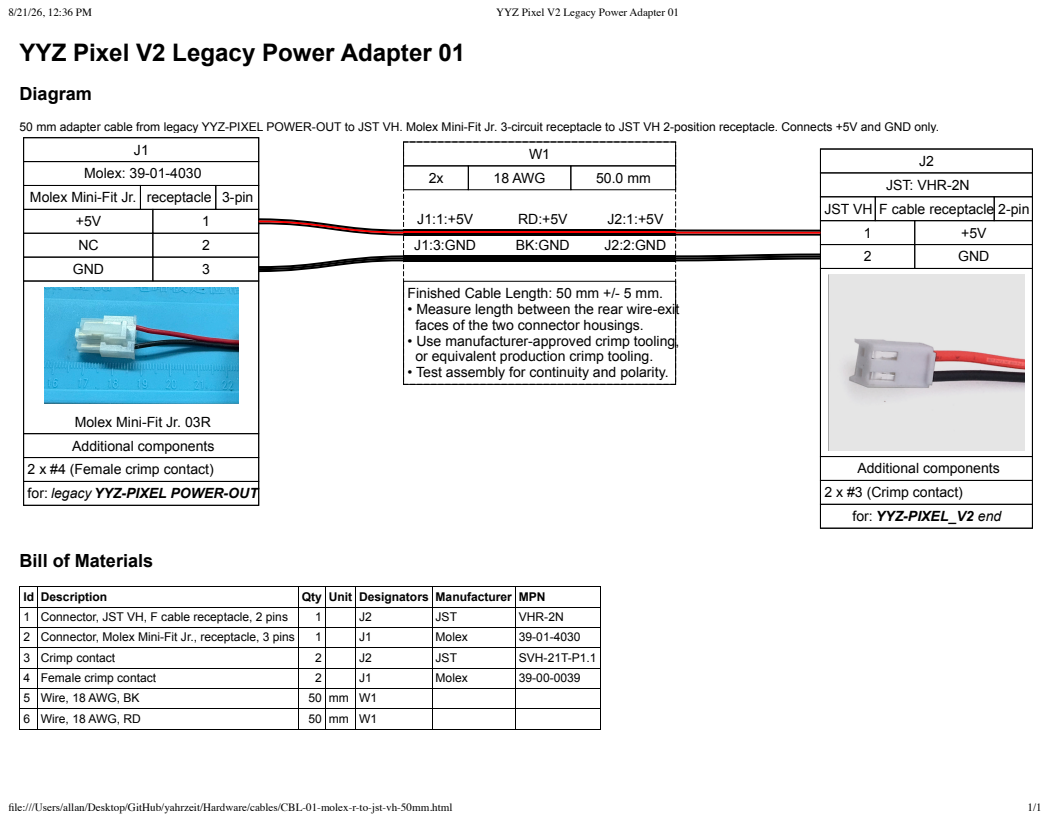
[picture p150: page 1]
J1 Molex: 39-01-4030; GND; 18 AWG; J1:3:GND; BK:GND; J2:2:GND; J2 JST: VHR-2N; YYZ Pixel V2 Legacy Power Adapter 01; file:///Users/allan/Desktop/GitHub/yahrzeit/Hardware/cables/CBL-01-molex-r-to-jst-vh-50mm.html

50 mm adapter cable from legacy YYZ-PIXEL POWER-OUT to JST VH. Molex Mini-Fit Jr. 3-circuit receptacle to JST VH 2-position receptacle. Connects +5V and GND only.

Molex Mini-Fit Jr. receptacle 3-pin

JST VH F cable receptacle 2-pin

Finished Cable Length: 50 mm +/- 5 mm.
• Measure length between the rear wire-exit
faces of the two connector housings.
• Use manufacturer-approved crimp tooling,
or equivalent production crimp tooling.
• Test assembly for continuity and polarity.

Molex Mini-Fit Jr. 03R
Additional components
2 x #4 (Female crimp contact)
for: legacyYYZ-PIXEL POWER-OUT

2 x #3 (Crimp contact)
for: YYZ-PIXEL_V2 end

Bill of Materials

Id | Description | Qty | Unit | Designators | Manufacturer | MPN
1 | Connector, JST VH, F cable receptacle, 2 pins | 1 | | J2 | JST | VHR-2N
2 | Connector, Molex Mini-Fit Jr., receptacle, 3 pins | 1 | | J1 | Molex | 39-01-4030
3 | Crimp contact | 2 | | J2 | JST | SVH-21T-P1.1
4 | Female crimp contact | 2 | | J1 | Molex | 39-00-0039
5 | Wire, 18 AWG, BK | 50 | mm | W1
6 | Wire, 18 AWG, RD | 50 | mm | W1
