allanschwartz/yahrzeit/embedded/yahrzeit_v3/YyzPixel.h

/**
 * @file        YyzPixel.h
 *
 * @brief       Device driver for the YYZ_PIXEL shift-register display chain.
 *
 *              This class owns the packed pixel framebuffer and knows how to
 *              shift that framebuffer into a chain of YYZ_PIXEL boards built
 *              from 74HC595-style serial-in / parallel-out registers.
 *
 *              Coordinates at this layer are zero-based. Higher-level
 *              one-based wall and panel mapping belongs to LedWall.
 *
 * @history     version 1.0 created for Congregation Beth Sholom, 2007-2008
 *              version 2.0 revised in July 2015
 *              version 3.0 revised in April 2026
 *
 * @author      Allan M. Schwartz, allanschwartz@sbcglobal.net
 *
 * @copyright   copyright (c) 2008,2015,2026, by Allan M. Schwartz
 *              All rights reserved.
 */

#pragma once

#include <Arduino.h>

class YyzPixel
{
public:

    // ----------------------------------------------------------------------------
    //            C O N S T R U C T O R
    // ----------------------------------------------------------------------------

    /**
     * @brief Construct the YYZ_PIXEL driver.
     */
    explicit YyzPixel(uint8_t dataPin, uint8_t oePin,
                      uint8_t cpPin, uint8_t stPin);


    // ----------------------------------------------------------------------------
    //            P U B L I C   F U N C T I O N S
    // ----------------------------------------------------------------------------

    /**
     * @brief   Initialize control pins with LED outputs blanked.
     */
    void begin();

    /**
     * @brief   Set or clear a pixel in the framebuffer.
     */
    void setPixel(uint16_t x, uint16_t y, uint8_t pixel);

    /**
     * @brief   Get a pixel value from the framebuffer.
     */
    bool getPixel(uint16_t x, uint16_t y) const;

    /**
     * @brief   Clear the framebuffer.
     */
    void clear();

    /**
     * @brief   Shift and latch the framebuffer into the physical display.
     */
    void refresh();

    /**
     * @brief   Toggle logical inversion of pixel output.
     */
    void reverse();

    /**
     * @brief   Check whether pixel output is active-low.
     */
    bool isActiveLow() const;

    /**
     * @brief   Set display brightness.
     */
    void setBrightness(uint8_t brightness);

    /**
     * @brief   Enable display output immediately at full brightness.
     */
    void on();

    /**
     * @brief   Blank display output without changing the framebuffer.
     */
    void off();

    /**
     * @brief   Save the complete fixed-size framebuffer to EEPROM.
     */
    void savePixels(int eepromOffset);

    /**
     * @brief   Load the complete fixed-size framebuffer from EEPROM.
     */
    void loadPixels(int eepromOffset);


private:

    // ----------------------------------------------------------------------------
    //            D A T A   M E M B E R S
    // ----------------------------------------------------------------------------

    uint8_t dataPin_;           // Arduino digital output connected to DI / SER.
    uint8_t oePin_;             // Arduino digital output connected to OE, active LOW.
    uint8_t cpPin_;             // Arduino digital output connected to CP / SRCLK.
    uint8_t stPin_;             // Arduino digital output connected to ST / RCLK.

    bool activeLow_ = true;     // true if shifted pixel data is active-low.
    bool displayOn_ = false;    // is the display ON or OFF
};
