allanschwartz/yahrzeit/embedded/yahrzeit_v3/selftest.ino

/**
 * @file        selftest.ino
 *
 * @brief       Self-test patterns for the Yahrzeit wall display.
 *
 *              These tests exercise the logical LedWall interface and,
 *              indirectly, the YYZ_PIXEL hardware driver underneath it.
 *              The tests are intended for bring-up, manufacturing checks,
 *              wiring verification, and field diagnostics. Startup also uses
 *              the marching-row pattern before restoring saved display data.
 *
 * @history     version 1.0 created for Congregation Beth Sholom, 2007-2008
 *              version 2.0 revised in July 2015
 *              version 3.0 revised in April 2026
 *
 * @author      Allan M. Schwartz, allanschwartz@sbcglobal.net
 *
 * @copyright   copyright (c) 2008,2015,2026, by Allan M. Schwartz
 *              All rights reserved.
 *
 * @notes       See project notes in yahrzeit_v3.h. These tests modify the
 *              framebuffer and may refresh the visible display. They do not
 *              save test patterns to EEPROM.
 */

#include "yahrzeit_v3.h"


// ----------------------------------------------------------------------------
//            P R I V A T E   F U N C T I O N S
// ----------------------------------------------------------------------------

/**
 * @brief   SELF TEST 1: turn on the four corner pixels.
 *
 * @param panel   PANEL0 for the whole display, or panel number 1..displayConfig.nPanels.
 *
 * @note This clears the selected display, then verifies both ends of the
 *       logical addressing range without lighting every pixel.
 */
static void selftestCorners(byte panel)
{
    ASSERT(panel <= displayConfig.nPanels);

    ResultIds rc = ledWall.allOn(0, panel);
    ASSERT(rc == NO_ERROR);

    if (panel == PANEL0) {
        // Exercise the full-wall coordinate path.
        ledWall.setPixel(1, 1, 1);
        ledWall.setPixel(1, displayConfig.nRows, 1);
        ledWall.setPixel(1, 1, displayConfig.nCols);
        ledWall.setPixel(1, displayConfig.nRows, displayConfig.nCols);
    } else {
        // Exercise the panel-local coordinate path.
        ledWall.setPixelInPanel(1, 1, 1, panel);
        ledWall.setPixelInPanel(1, ledWall.rowsInPanel(panel), 1, panel);
        ledWall.setPixelInPanel(1, 1, ledWall.colsInPanel(panel), panel);
        ledWall.setPixelInPanel(1, ledWall.rowsInPanel(panel),
                                ledWall.colsInPanel(panel), panel);
    }

    // intentional visible pacing for operator observation
    sleepMs(true, 500);
}

/**
 * @brief   SELF TEST 2/3 helper: turn all pixels on or off.
 *
 * @param pixelBit   false = off, true = on.
 * @param panel      PANEL0 for the whole display, or panel number 1..displayConfig.nPanels.
 */
static void selftestAllOn(bool pixelBit, byte panel)
{
    ASSERT(panel <= displayConfig.nPanels);

    ResultIds rc = ledWall.allOn(0, panel);
    ASSERT(rc == NO_ERROR);

    if (panel == PANEL0) {
        for (byte col = 1; col <= displayConfig.nCols; ++col) {
            for (byte row = 1; row <= displayConfig.nRows; ++row) {
                const ResultIds rc = ledWall.setPixel(pixelBit, row, col);
                ASSERT(rc == NO_ERROR);
            }
        }
    } else {
        for (byte col = 1; col <= ledWall.colsInPanel(panel); ++col) {
            for (byte row = 1; row <= ledWall.rowsInPanel(panel); ++row) {
                const ResultIds rc = ledWall.setPixelInPanel(pixelBit, row, col, panel);
                ASSERT(rc == NO_ERROR);
            }
        }
    }

    // intentional visible pacing for operator observation
    sleepMs(true, 500);
}

/**
 * @brief   SELF TEST 4: checkerboard pattern.
 *
 * Alternates pixels across rows and columns.  This is more diagnostic than
 * a simple all-on/all-off flash because adjacent pixels are driven to opposite
 * states.
 *
 * @param panel   PANEL0 for the whole display, or panel number 1..displayConfig.nPanels.
 *
 * @note This test is useful for finding row/column swaps, off-by-one mapping
 *       errors, and adjacent-bit coupling or ghosting.
 */
static void selftestCheckerboard(byte panel)
{
    ASSERT(panel <= displayConfig.nPanels);

    ResultIds rc = ledWall.allOn(0, panel);
    ASSERT(rc == NO_ERROR);

    static bool invertPattern = false;

    const byte nRows = (panel == PANEL0)
                     ? displayConfig.nRows
                     : ledWall.rowsInPanel(panel);

    const byte nCols = (panel == PANEL0)
                     ? displayConfig.nCols
                     : ledWall.colsInPanel(panel);

    for (byte row = 1; row <= nRows; ++row) {
        for (byte col = 1; col <= nCols; ++col) {
            const bool pixel = ((row + col) & 1) ^ invertPattern;

            if (panel == PANEL0) {
                ledWall.setPixel(pixel, row, col);
            } else {
                ledWall.setPixelInPanel(pixel, row, col, panel);
            }
        }
    }

    invertPattern = !invertPattern;

    // intentional visible pacing for operator observation
    sleepMs(true, 500);
}

/**
 * @brief   SELF TEST 5: marching-row pattern.
 *
 * For PANEL0, each logical wall row is displayed once across the full wall.
 * A specific panel number limits the pattern to that panel's local rows and
 * columns.
 *
 * @param panel   PANEL0 for the whole display, or panel number
 *                1..displayConfig.nPanels
 */
void selftestMarchingRow(byte panel)
{
    ASSERT(panel <= displayConfig.nPanels);

    ResultIds rc = ledWall.allOn(0, panel);
    ASSERT(rc == NO_ERROR);

    const byte nRows = (panel == PANEL0)
                     ? displayConfig.nRows
                     : ledWall.rowsInPanel(panel);

    const byte nCols = (panel == PANEL0)
                     ? displayConfig.nCols
                     : ledWall.colsInPanel(panel);

    for (byte row = 1; row <= nRows; ++row) {
        for (byte col = 1; col <= nCols; ++col) {
            const ResultIds rc = (panel == PANEL0)
                               ? ledWall.setPixel(1, row, col)
                               : ledWall.setPixelInPanel(1, row, col, panel);
            ASSERT(rc == NO_ERROR);
        }

        sleepMs(true, 300);

        for (byte col = 1; col <= nCols; ++col) {
            const ResultIds rc = (panel == PANEL0)
                               ? ledWall.setPixel(0, row, col)
                               : ledWall.setPixelInPanel(0, row, col, panel);
            ASSERT(rc == NO_ERROR);
        }

        sleepMs(true, 1);
    }

    sleepMs(true, 500);
}

/**
 * @brief   SELF TEST 6: marching column pattern.
 *
 * Turns on one column at a time, pauses, then turns that column off before
 * moving to the next column.
 *
 * @param panel   PANEL0 for the whole display, or panel number 1..displayConfig.nPanels.
 */
static void selftestMarchingCol(byte panel)
{
    ASSERT(panel <= displayConfig.nPanels);

    ResultIds rc = ledWall.allOn(0, panel);
    ASSERT(rc == NO_ERROR);

    for (byte col = 1; col <= ledWall.colsInPanel(panel); ++col) {
        for (byte row = 1; row <= ledWall.rowsInPanel(panel); ++row) {
            const ResultIds rc = ledWall.setPixelInPanel(1, row, col, panel);
            ASSERT(rc == NO_ERROR);
        }

        sleepMs(true, 300);

        for (byte row = 1; row <= ledWall.rowsInPanel(panel); ++row) {
            const ResultIds rc = ledWall.setPixelInPanel(0, row, col, panel);
            ASSERT(rc == NO_ERROR);
        }

        sleepMs(true, 1);
    }

    // intentional visible pacing for operator observation
    sleepMs(true, 500);
}


/**
 * @brief   Print a one-line description of the selected self-test.
 *
 * @param streamID          output stream, such as SOCKET or CONSOLE.
 * @param testNumber        self-test number.
 * @param testDescription   human-readable test description.
 * @param panel             PANEL0 for whole display, or panel number 1..displayConfig.nPanels.
 */
static void selftestDescription(byte streamID,
                                 byte testNumber,
                                 const char *testDescription,
                                 byte panel)
{
    if (panel > PANEL0) {
        snprintf(outputBuf, sizeof outputBuf,
                 "selftest %d - %s panel %d\n",
                 testNumber, testDescription, panel);
    } else {
        snprintf(outputBuf, sizeof outputBuf,
                 "selftest %d - %s\n",
                 testNumber, testDescription);
    }

    writeOutput(streamID, outputBuf);
}


// ----------------------------------------------------------------------------
//            P U B L I C   F U N C T I O N S
// ----------------------------------------------------------------------------

/**
 * @brief   Dispatch one of the LED self-test patterns.
 *
 * The command interface supports:
 *
 *      TEst 1 [panel]   four corner pixels on
 *      TEst 2 [panel]   all pixels on
 *      TEst 3 [panel]   all pixels off
 *      TEst 4 [panel]   checkerboard pattern
 *      TEst 5           marching row pattern across every panel
 *      TEst 6 [panel]   marching column pattern
 *
 * If panel is omitted by the command layer, PANEL0 is used and the test
 * applies to the entire active display.
 *
 * @param streamID     output stream, such as SOCKET or CONSOLE.
 * @param testNumber   self-test number, 1..6.
 * @param panel        PANEL0 for whole display, or panel number
 *                     1..displayConfig.nPanels; test 5 currently ignores it
 *
 * @returns            NO_ERROR, ERR_PANEL, or ERR_TESTNUM.
 */
ResultIds selftest(byte streamID, byte testNumber, byte panel)
{
    if (panel > displayConfig.nPanels) {
        return ERR_PANEL;
    }

    switch (testNumber) {
        case 1:
            selftestDescription(streamID, testNumber,
                                    "corner pixels on", panel);
            selftestCorners(panel);
            break;

        case 2:
            selftestDescription(streamID, testNumber,
                                    "turn pixels ON", panel);
            selftestAllOn(1, panel);
            break;

        case 3:
            selftestDescription(streamID, testNumber,
                                    "turn pixels OFF", panel);
            selftestAllOn(0, panel);
            break;

        case 4:
            selftestDescription(streamID, testNumber,
                                    "checkerboard pattern", panel);
            selftestCheckerboard(panel);
            break;

        case 5:
            selftestDescription(streamID, testNumber,
                                    "marching row pattern", panel);
            selftestMarchingRow(panel);
            break;

        case 6:
            selftestDescription(streamID, testNumber,
                                    "marching column pattern", panel);
            selftestMarchingCol(panel);
            break;

        default:
            return ERR_TESTNUM;
    }

    return NO_ERROR;
}
